taylorjsam/3D-Printed-Wall-Control/Printed Snap Hook Hangers/Park Tool/Park Tool CT-3 (vert) PH.stl

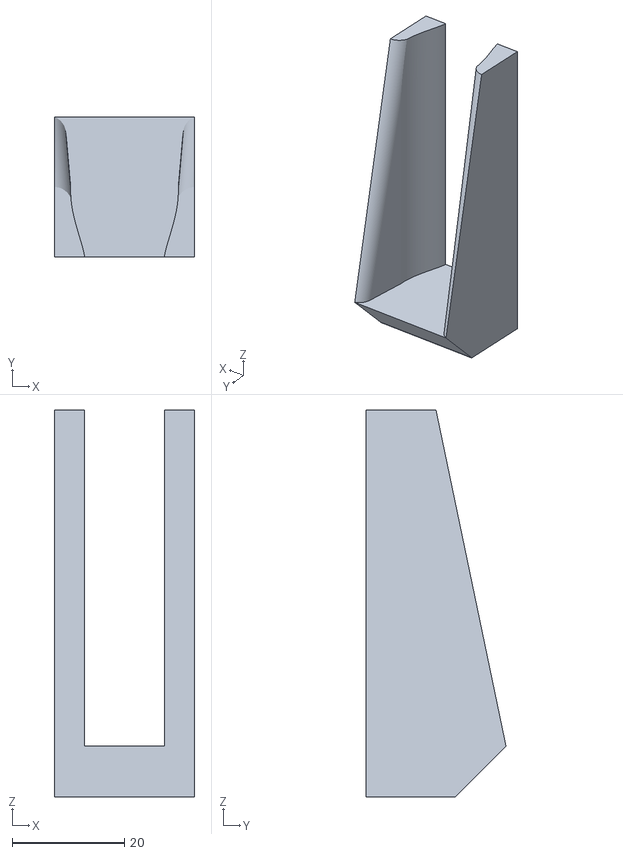
[picture p15: CAD file, 2025-12-08]
Printed Snap Hook Hangers/Park Tool/Park Tool CT-3 (vert) PH.stl
25.0 x 25.0 x 69.1
