taylorjsam/3D-Printed-Wall-Control/Printed Snap Hook Hangers/PB Swiss/PB Swiss 1255 MR PH.stl

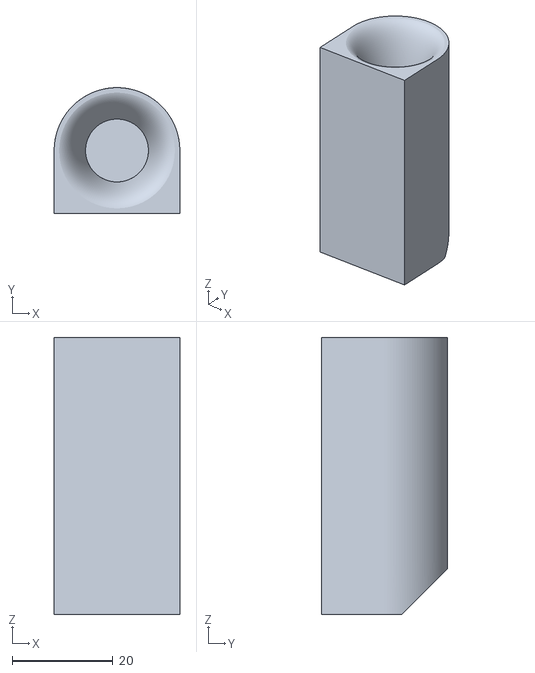
[picture p16: CAD file, 2025-11-05]
Printed Snap Hook Hangers/PB Swiss/PB Swiss 1255 MR PH.stl
25.0 x 25.0 x 55.1
