taylorjsam/3D-Printed-Wall-Control/Printed Snap Hook Hangers/Pedro's/Pedros Cable Cutters (vert)PH.stl

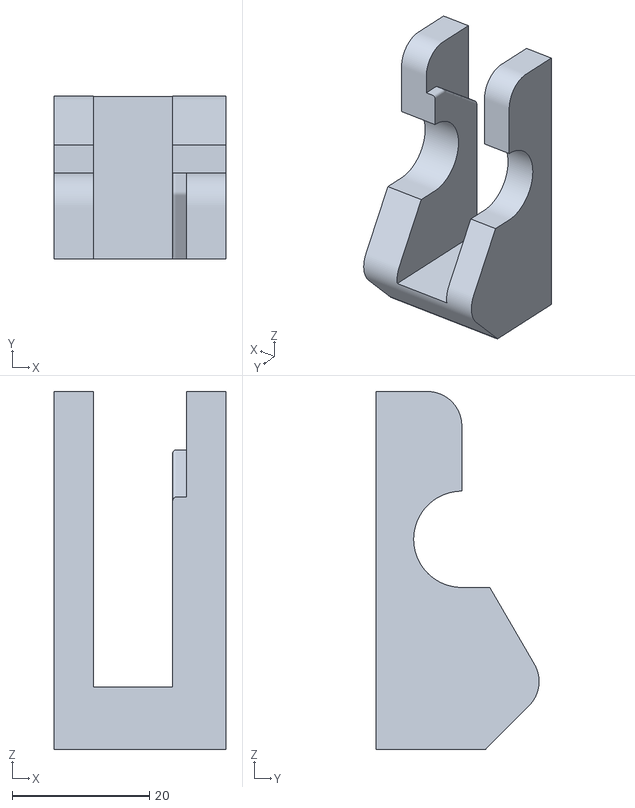
[picture p17: CAD file, 2025-11-06]
Printed Snap Hook Hangers/Pedro's/Pedros Cable Cutters (vert)PH.stl
25.0 x 23.7 x 52.1
