taylorjsam/3D-Printed-Wall-Control/Printed Snap Hook Hangers/Rock Shox/Rock Shox Shock Pump SH.stl

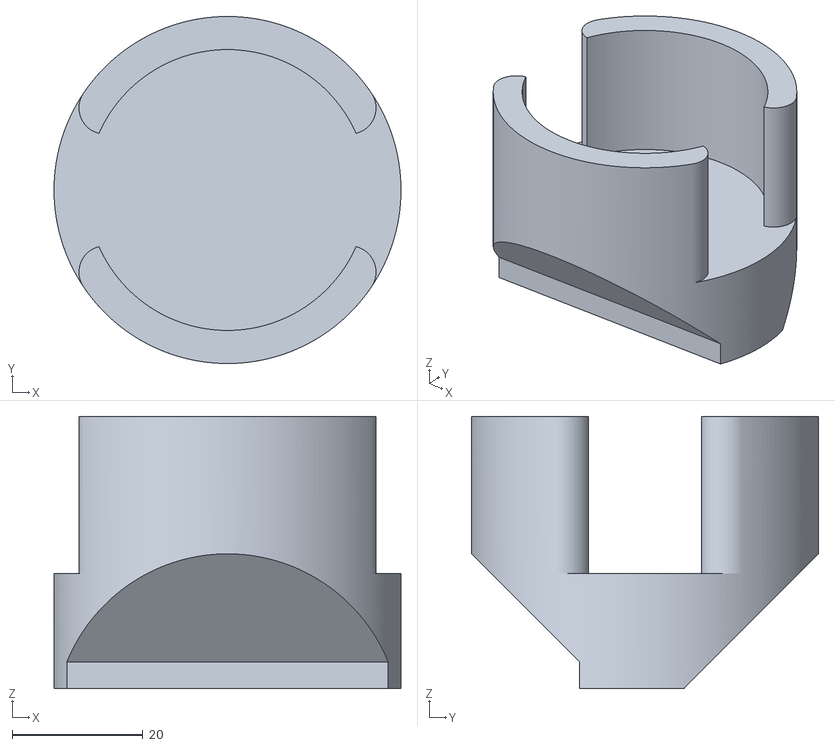
[picture p18: CAD file, 2025-10-18]
Printed Snap Hook Hangers/Rock Shox/Rock Shox Shock Pump SH.stl
53.0 x 53.0 x 41.6
