taylorjsam/3D-Printed-Wall-Control/Printed Snap Hook Hangers/Shimano/Shimano Bleed Funnel PH.stl

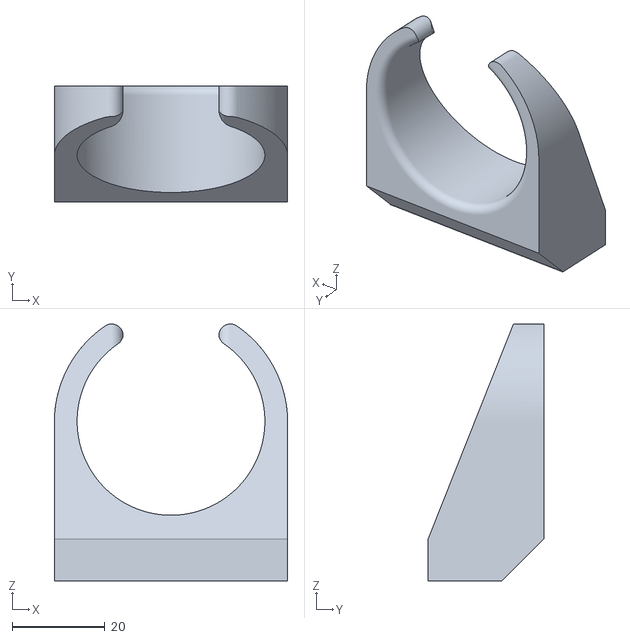
[picture p19: CAD file, 2025-12-08]
Printed Snap Hook Hangers/Shimano/Shimano Bleed Funnel PH.stl
50.4 x 25.0 x 55.5
