taylorjsam/3D-Printed-Wall-Control/Printed Snap Hook Hangers/SK/SK 10 Heavy Duty Scissors PH.stl

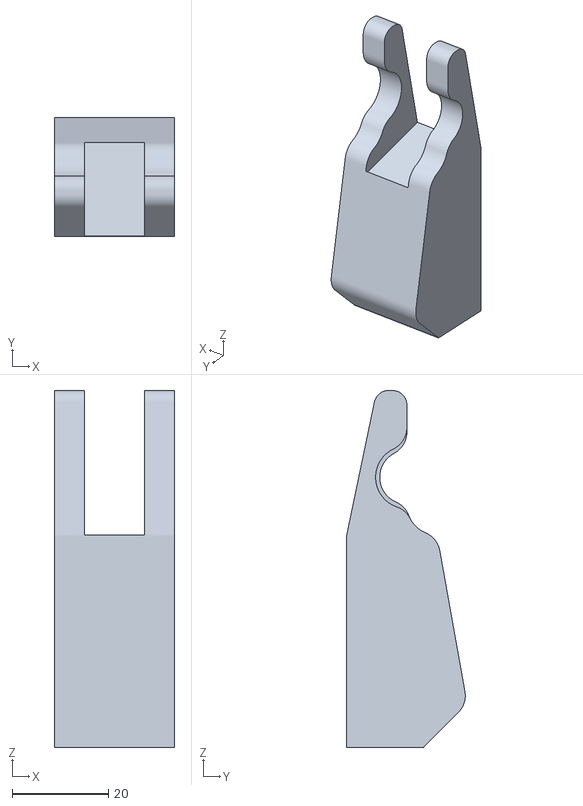
[picture p20: CAD file, 2025-10-25]
Printed Snap Hook Hangers/SK/SK 10 Heavy Duty Scissors PH.stl
25.0 x 24.6 x 74.1
