taylorjsam/3D-Printed-Wall-Control/Printed Snap Hook Hangers/Stan's/Stan's 2oz Bottle.stl

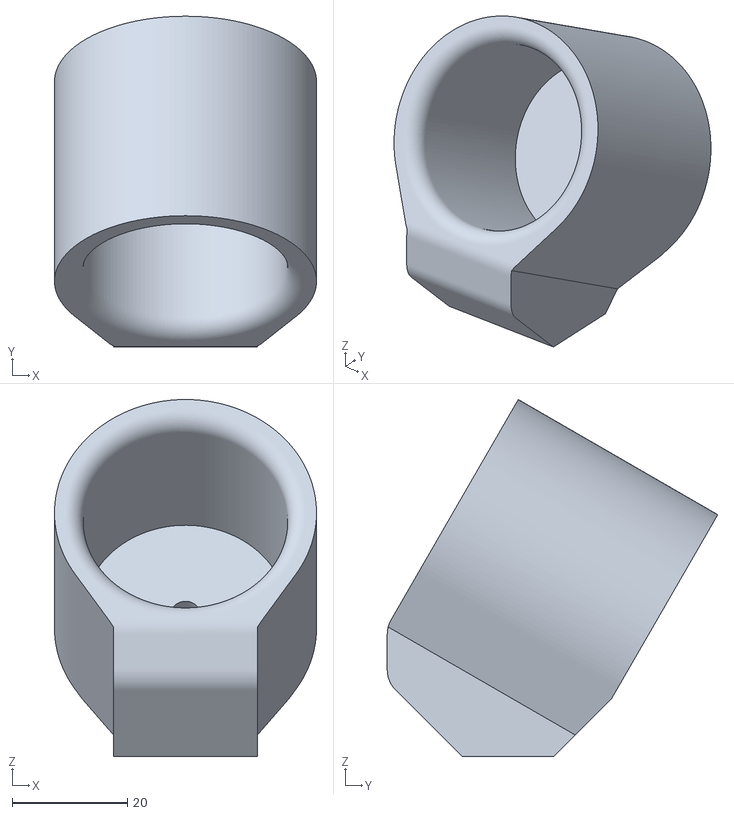
[picture p21: CAD file, 2025-12-18]
Printed Snap Hook Hangers/Stan's/Stan's 2oz Bottle.stl
45.5 x 57.4 x 62.0
