taylorjsam/3D-Printed-Wall-Control/Printed Snap Hook Hangers/Starrett/Starrett 18-C.stl

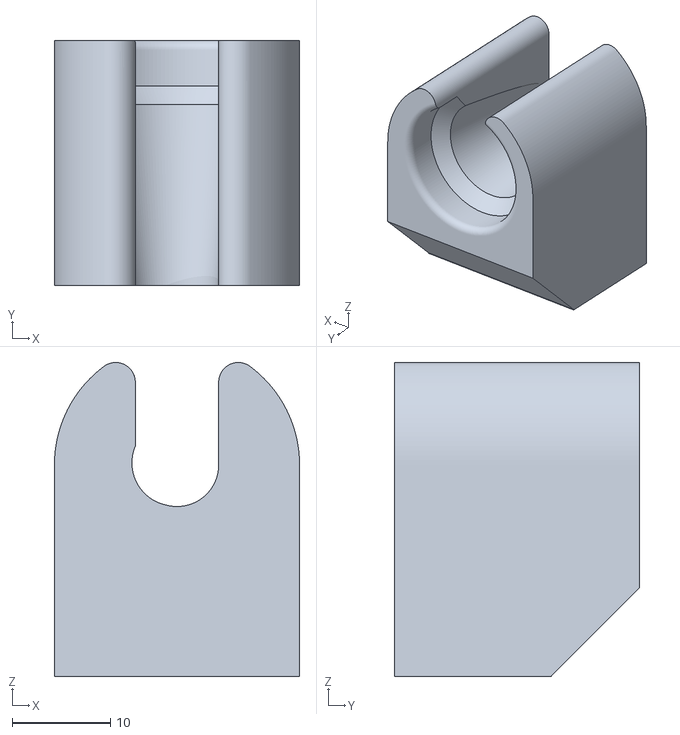
[picture p22: CAD file, 2026-03-05]
Printed Snap Hook Hangers/Starrett/Starrett 18-C.stl
25.0 x 25.0 x 32.0
