taylorjsam/3D-Printed-Wall-Control/Printed Snap Hook Hangers/Vessel/Vessel Megadora 6pc PH.stl

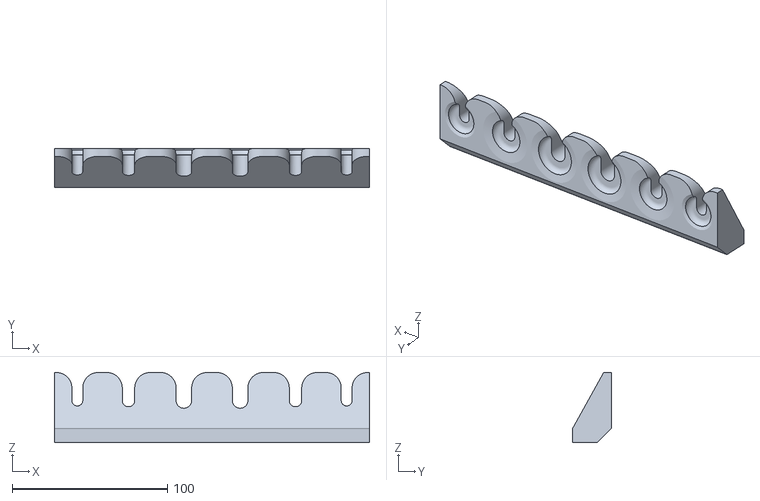
[picture p23: CAD file, 2025-10-19]
Printed Snap Hook Hangers/Vessel/Vessel Megadora 6pc PH.stl
202.8 x 25.0 x 45.1
