taylorjsam/3D-Printed-Wall-Control/Printed Snap Hook Hangers/Wera/Wera 074710 (Adjustable Torque) PH.stl

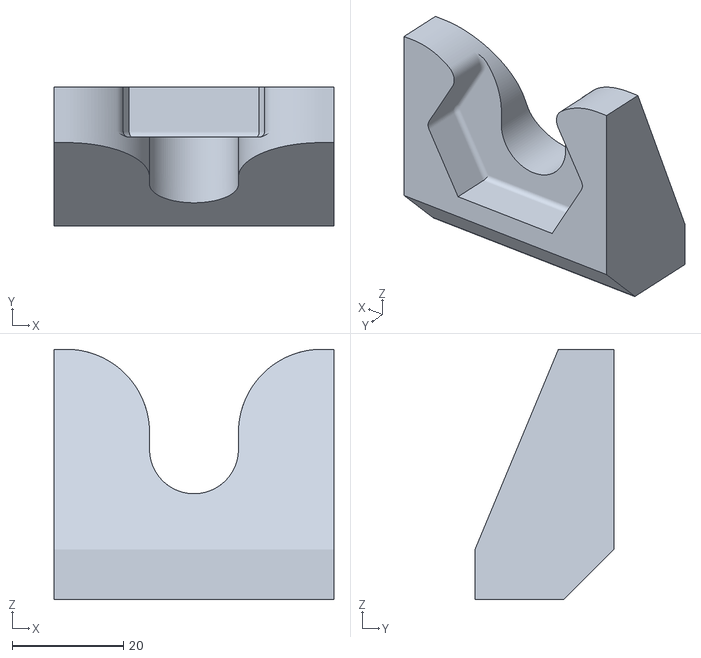
[picture p24: CAD file, 2026-03-10]
Printed Snap Hook Hangers/Wera/Wera 074710 (Adjustable Torque) PH.stl
50.4 x 25.0 x 45.1
