taylorjsam/3D-Printed-Wall-Control/Wall Control Paint Hook/Bernzomatic/Bernzomatic Firepoint Creator Tool.stl

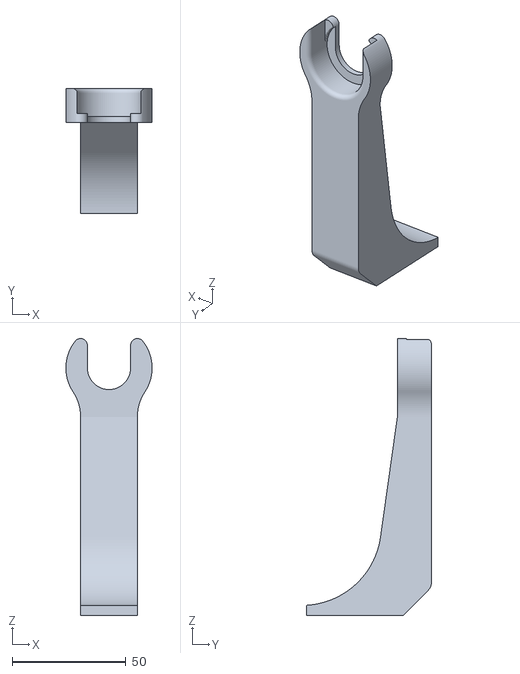
[picture p25: CAD file, 2025-12-18]
Wall Control Paint Hook/Bernzomatic/Bernzomatic Firepoint Creator Tool.stl
38.0 x 55.0 x 122.0
