taylorjsam/3D-Printed-Wall-Control/Wall Control Paint Hook/Milwaukee/M18 Upright v4 (long).stl

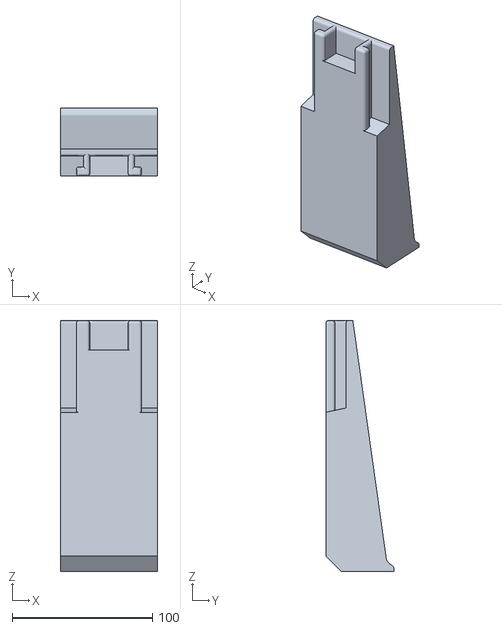
[picture p26: CAD file, 2025-12-08]
Wall Control Paint Hook/Milwaukee/M18 Upright v4 (long).stl
69.0 x 48.8 x 179.0
