taylorjsam/3D-Printed-Wall-Control/Wall Control Small Hook/CooBeast/CooBeast 1:4 Digital Torque Wrench.stl

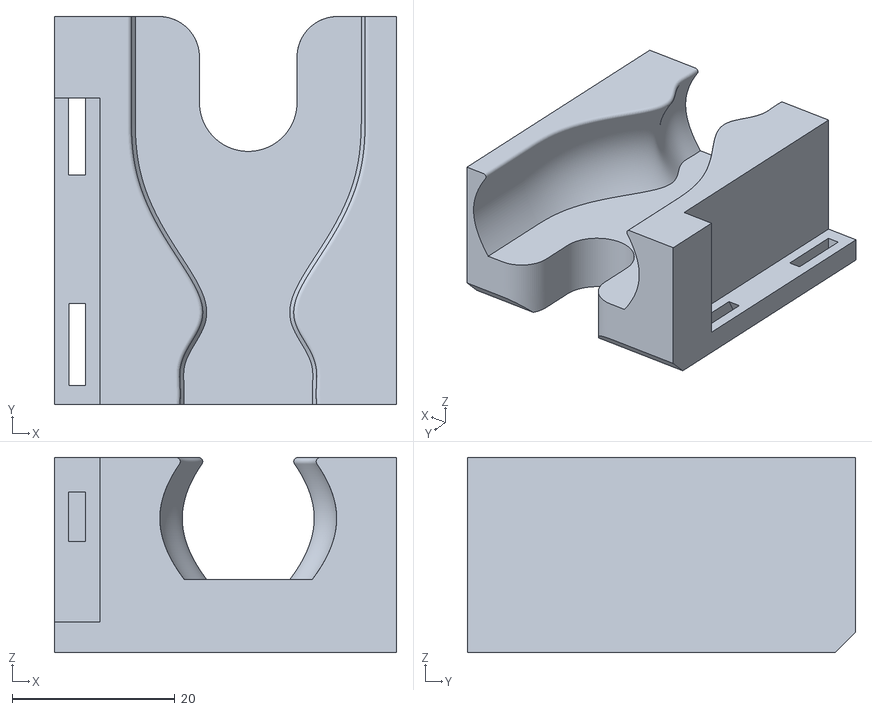
[picture p27: CAD file, 2025-12-20]
Wall Control Small Hook/CooBeast/CooBeast 1:4 Digital Torque Wrench.stl
42.1 x 47.8 x 24.0
