taylorjsam/3D-Printed-Wall-Control/Wall Control Small Hook/epAuto/epAuto 1:2 Torque Wrench.stl

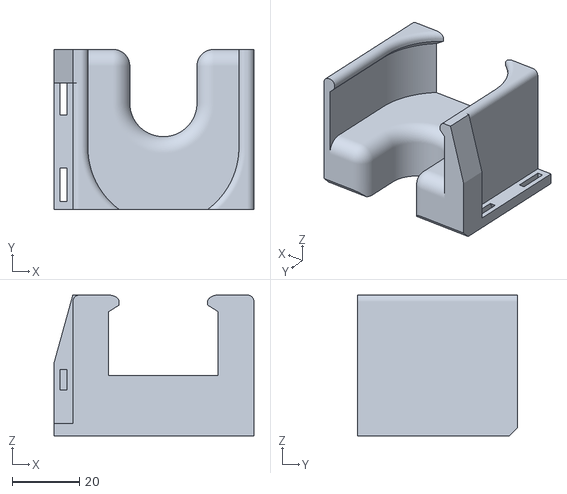
[picture p28: CAD file, 2025-12-20]
Wall Control Small Hook/epAuto/epAuto 1:2 Torque Wrench.stl
59.6 x 47.8 x 42.0
