taylorjsam/3D-Printed-Wall-Control/Wall Control Small Hook/Generic/Angle Grinder Disc Holder v1.stl

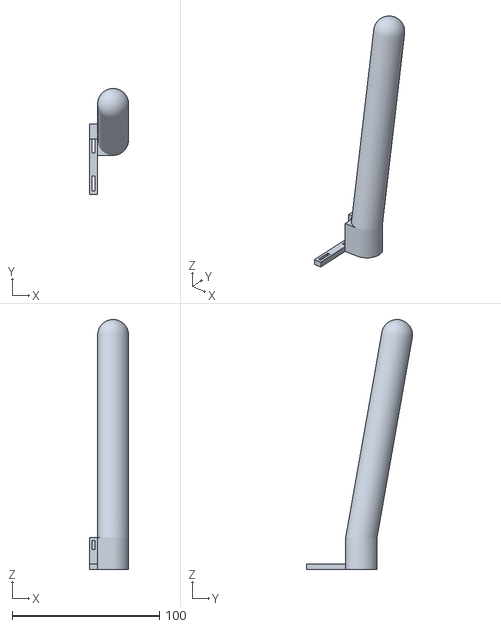
[picture p29: CAD file, 2025-12-08]
Wall Control Small Hook/Generic/Angle Grinder Disc Holder v1.stl
26.6 x 72.0 x 169.6
