taylorjsam/3D-Printed-Wall-Control/Wall Control Small Hook/Ignance/Igance P6 Pro (Single).stl

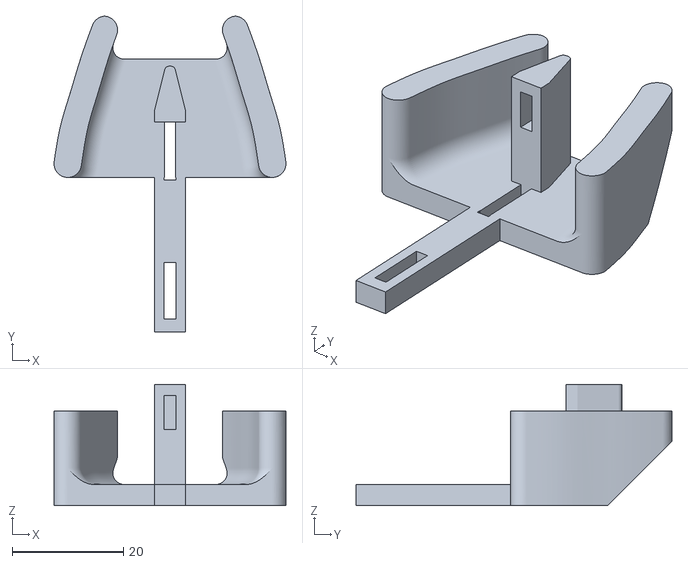
[picture p30: CAD file, 2025-10-04]
Wall Control Small Hook/Ignance/Igance P6 Pro (Single).stl
41.7 x 56.7 x 21.8
