taylorjsam/3D-Printed-Wall-Control/Wall Control Small Hook/Knipex/Knipex Electrician Shears.stl

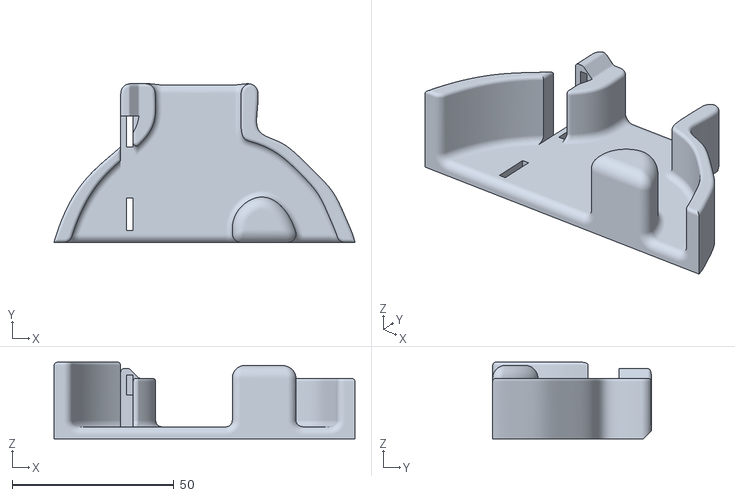
[picture p31: CAD file, 2025-12-08]
Wall Control Small Hook/Knipex/Knipex Electrician Shears.stl
93.1 x 49.0 x 23.8
