taylorjsam/3D-Printed-Wall-Control/Wall Control Small Hook/Park Tool/Park Tool HMR-4.stl

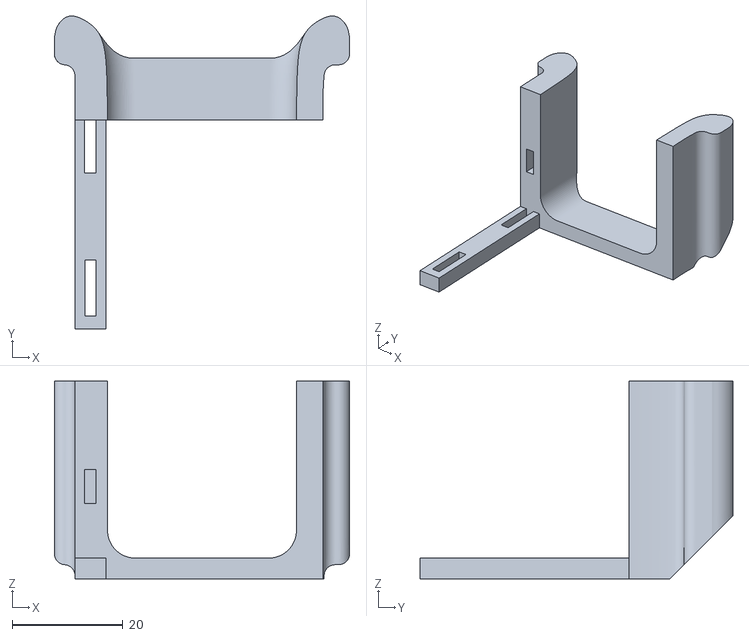
[picture p32: CAD file, 2025-10-07]
Wall Control Small Hook/Park Tool/Park Tool HMR-4.stl
53.4 x 56.6 x 35.8
