taylorjsam/3D-Printed-Wall-Control/Wall Control Small Hook/Pedros/Pedros Cable Cutters.stl

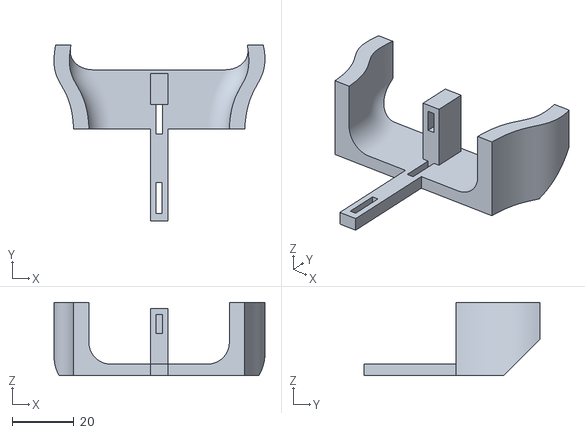
[picture p33: CAD file, 2025-10-04]
Wall Control Small Hook/Pedros/Pedros Cable Cutters.stl
68.4 x 57.0 x 23.8
