taylorjsam/3D-Printed-Wall-Control/Wall Control Small Hook/Rock Shox/Rock Shox Shock Pump.stl

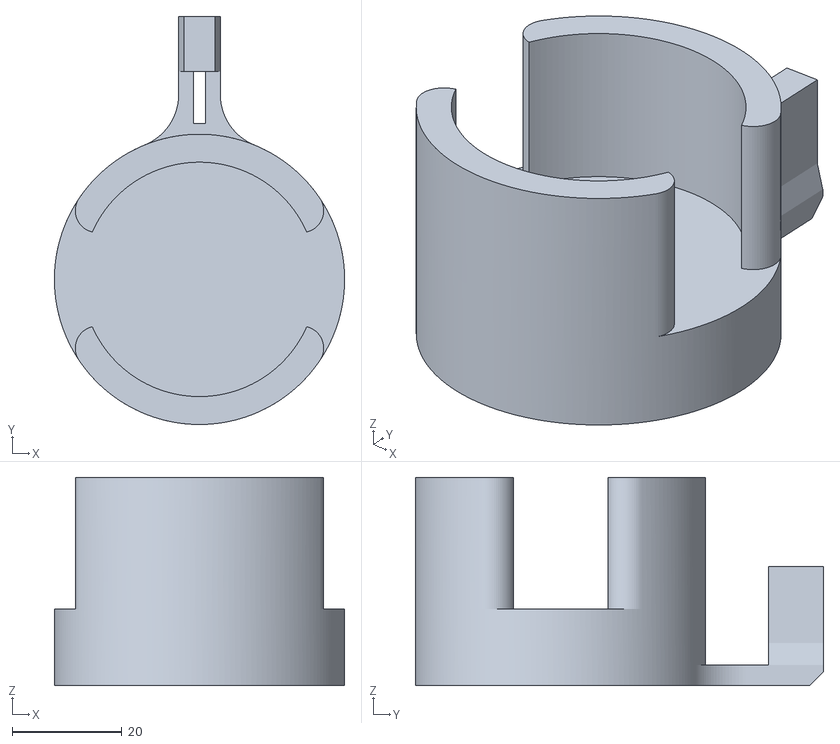
[picture p34: CAD file, 2025-10-04]
Wall Control Small Hook/Rock Shox/Rock Shox Shock Pump.stl
53.0 x 74.5 x 38.0
