taylorjsam/3D-Printed-Wall-Control/Wall Control Small Hook/SK/SK 8in Shears.stl

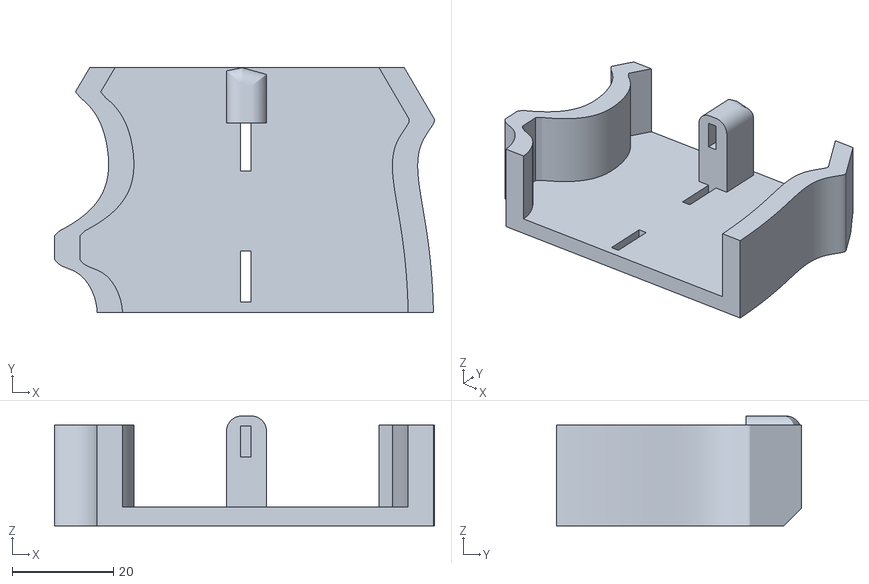
[picture p35: CAD file, 2025-10-10]
Wall Control Small Hook/SK/SK 8in Shears.stl
75.2 x 48.4 x 21.8
