taylorjsam/3D-Printed-Wall-Control/Wall Control Small Hook/Wera/Wera Hex Plus Allen Set.stl

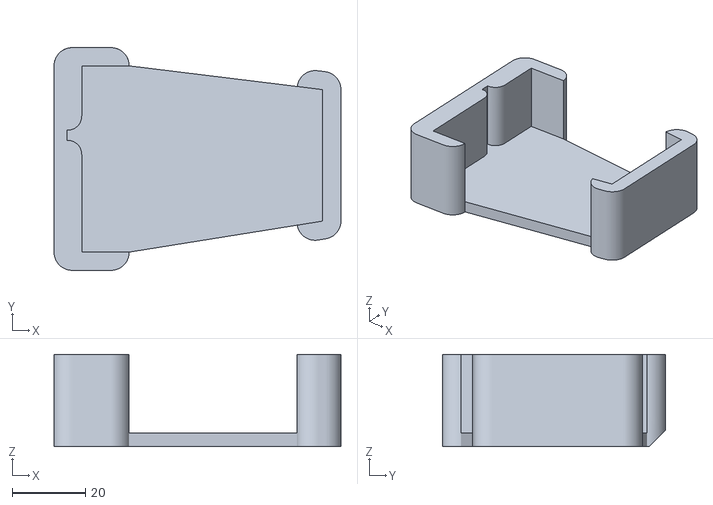
[picture p36: CAD file, 2025-10-07]
Wall Control Small Hook/Wera/Wera Hex Plus Allen Set.stl
78.6 x 61.0 x 25.3
