taylorjsam/3D-Printed-Wall-Control/Printed Snap Hook Hangers/Generic/Adjustable Wrenches/Adjustable Wrench 10mm (vert) PH.stl

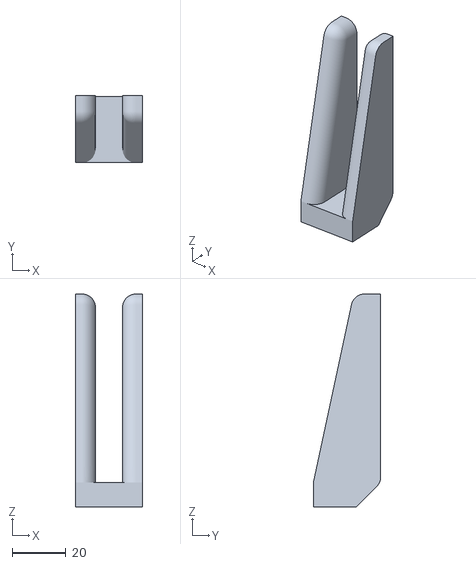
[picture p37: CAD file, 2025-12-08]
Printed Snap Hook Hangers/Generic/Adjustable Wrenches/Adjustable Wrench 10mm (vert) PH.stl
25.0 x 25.0 x 79.1
