taylorjsam/3D-Printed-Wall-Control/Printed Snap Hook Hangers/Generic/Socket Drive Accessories/2x 1:4 Drive Male Narrow.stl

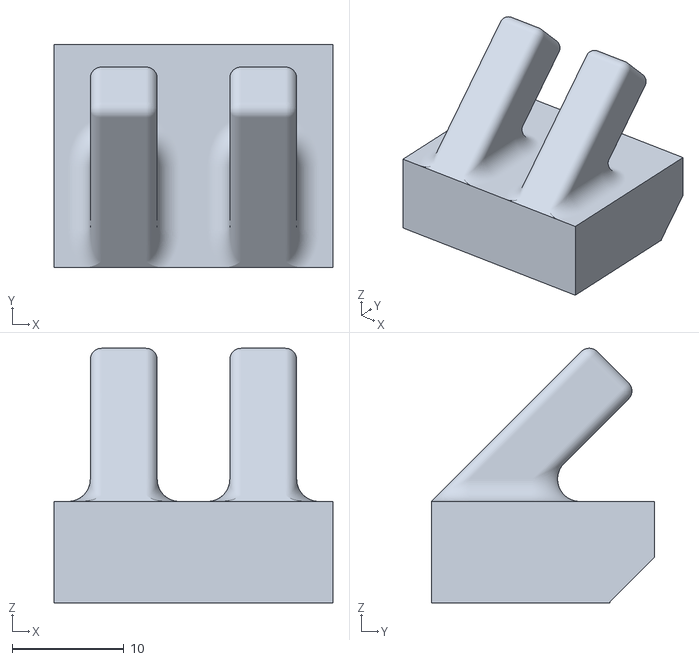
[picture p38: CAD file, 2025-12-20]
Printed Snap Hook Hangers/Generic/Socket Drive Accessories/2x 1:4 Drive Male Narrow.stl
25.0 x 20.0 x 22.8
