taylorjsam/3D-Printed-Wall-Control/Printed Snap Hook Hangers/Knipex/Knipex 8551250 (vert) PH.stl

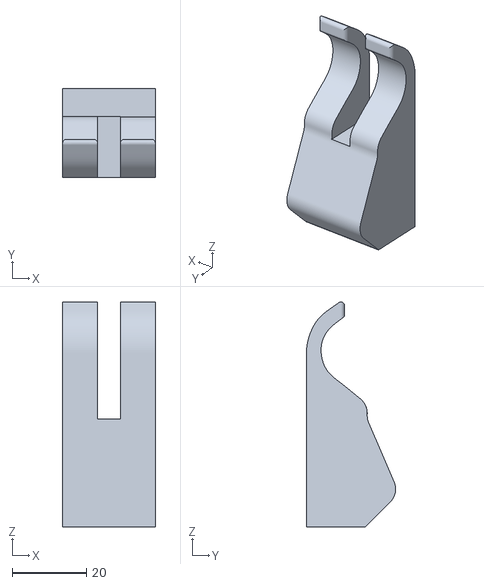
[picture p39: CAD file, 2025-10-23]
Printed Snap Hook Hangers/Knipex/Knipex 8551250 (vert) PH.stl
25.0 x 24.1 x 60.7
