taylorjsam/3D-Printed-Wall-Control/Printed Snap Hook Hangers/Milwaukee/Milwaukee 48-22-3410 PH.stl.stl

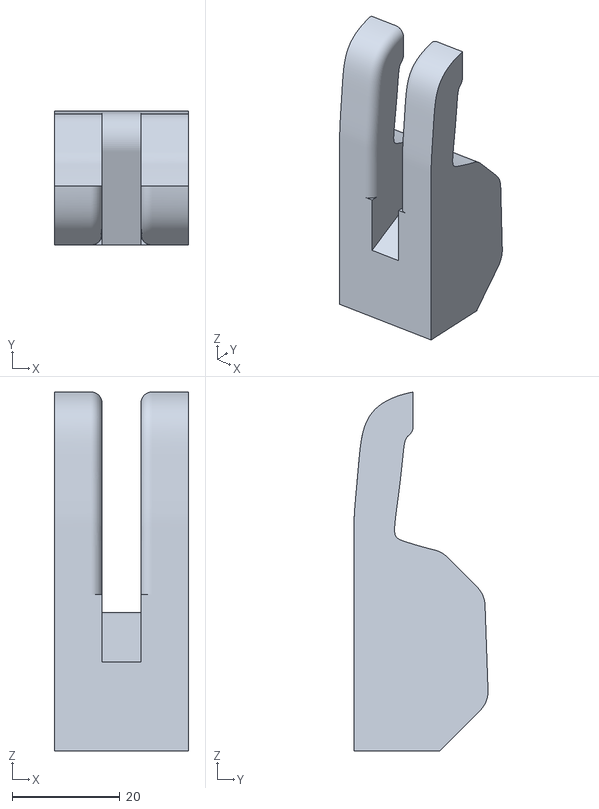
[picture p40: CAD file, 2025-10-25]
Printed Snap Hook Hangers/Milwaukee/Milwaukee 48-22-3410 PH.stl.stl
25.0 x 24.9 x 66.7
