taylorjsam/3D-Printed-Wall-Control/Printed Snap Hook Hangers/Park Tool/Park Tool CT-3 PH.stl

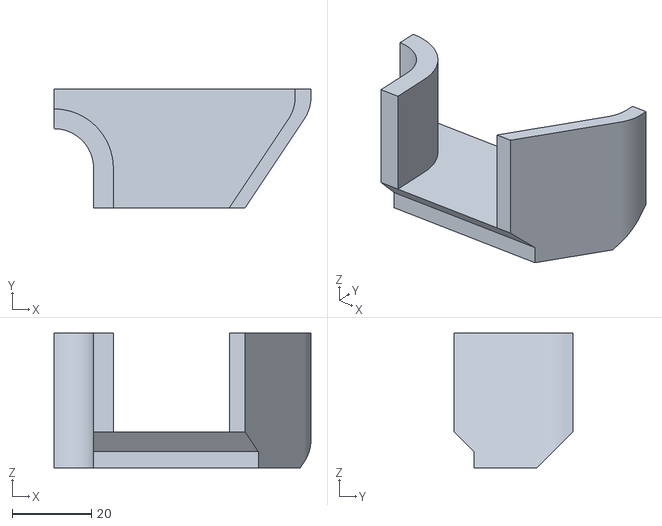
[picture p41: CAD file, 2025-11-06]
Printed Snap Hook Hangers/Park Tool/Park Tool CT-3 PH.stl
65.0 x 30.0 x 34.1
