taylorjsam/3D-Printed-Wall-Control/Printed Snap Hook Hangers/PB Swiss/PB Swiss 4pc PH-PZ PH.stl

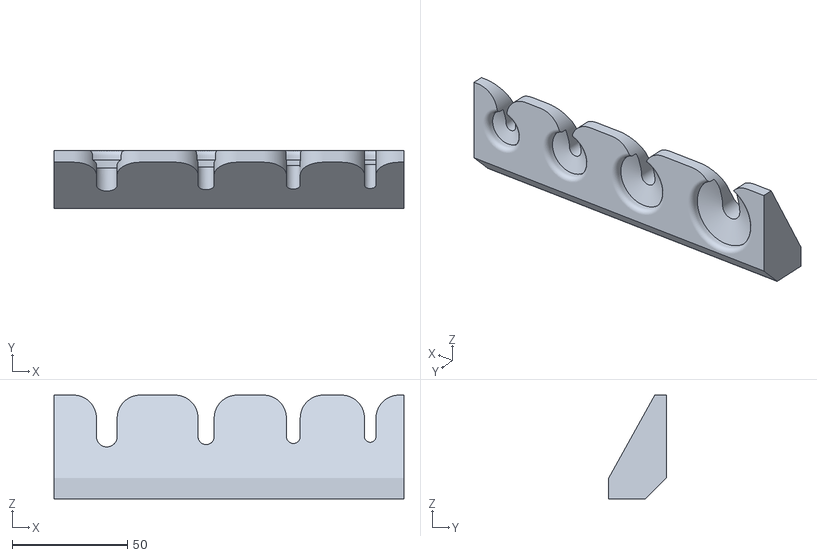
[picture p42: CAD file, 2025-10-24]
Printed Snap Hook Hangers/PB Swiss/PB Swiss 4pc PH-PZ PH.stl
152.0 x 25.0 x 45.1
