taylorjsam/3D-Printed-Wall-Control/Printed Snap Hook Hangers/Pedro's/Pedro's Downhill Tire Lever.stl

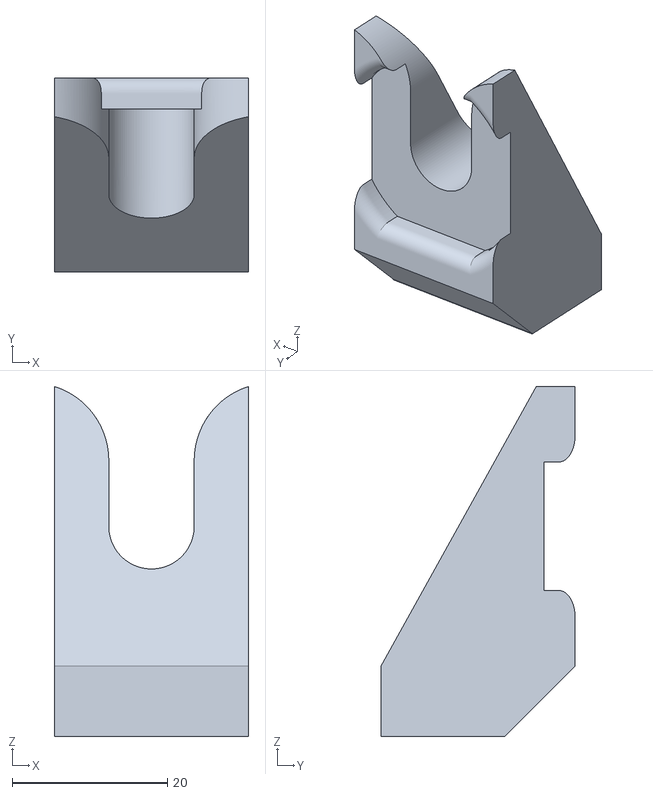
[picture p43: CAD file, 2025-10-18]
Printed Snap Hook Hangers/Pedro's/Pedro's Downhill Tire Lever.stl
25.0 x 25.0 x 45.1
