taylorjsam/3D-Printed-Wall-Control/Printed Snap Hook Hangers/SK/SK 8" Heavy Duty Cutters PH.stl

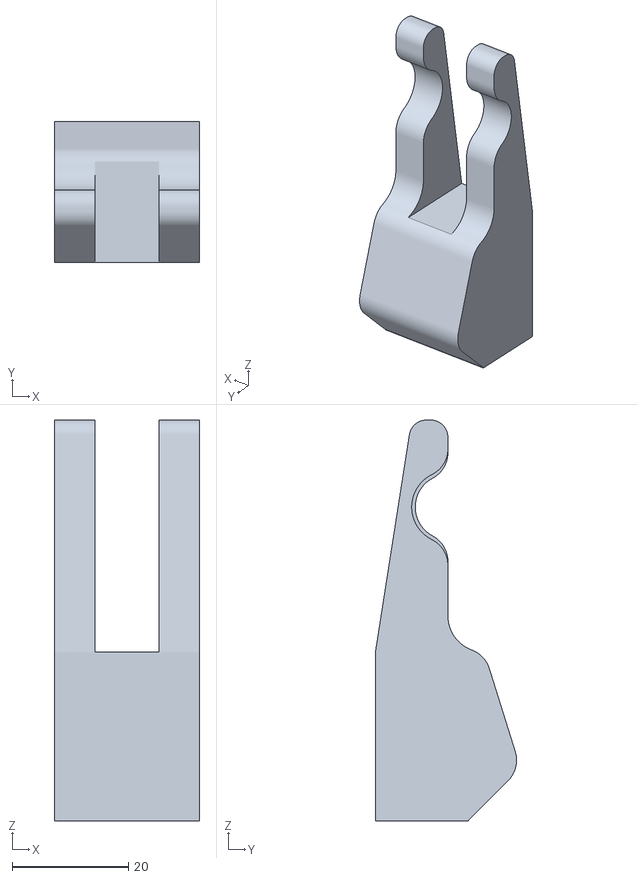
[picture p44: CAD file, 2025-10-24]
Printed Snap Hook Hangers/SK/SK 8" Heavy Duty Cutters PH.stl
25.0 x 24.3 x 69.1
