taylorjsam/3D-Printed-Wall-Control/Printed Snap Hook Hangers/Snap On/Snap On AWSG800 PH.stl

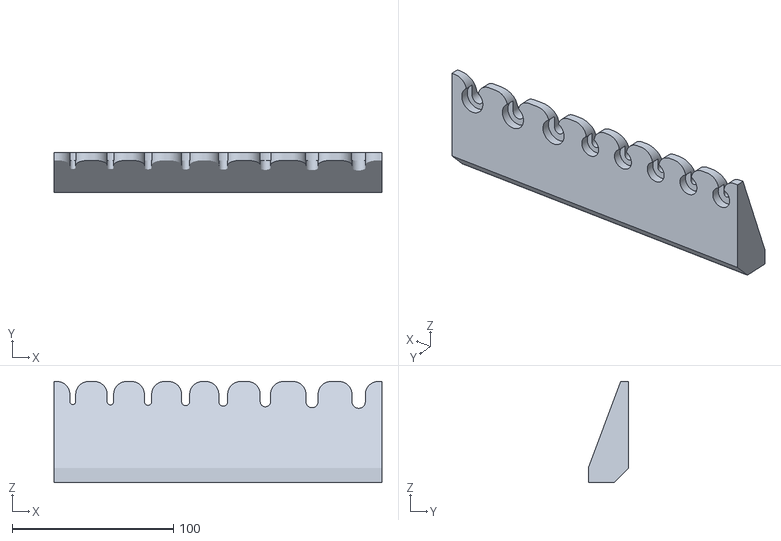
[picture p45: CAD file, 2025-11-05]
Printed Snap Hook Hangers/Snap On/Snap On AWSG800 PH.stl
203.2 x 25.0 x 62.6
