taylorjsam/3D-Printed-Wall-Control/Printed Snap Hook Hangers/Stan's/Stan's Core Remover.stl

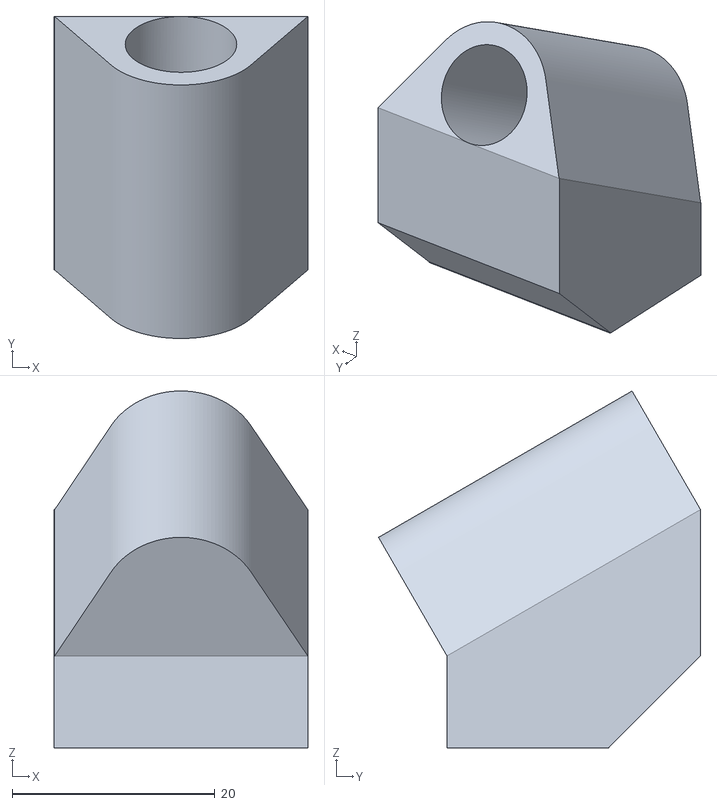
[picture p46: CAD file, 2025-10-18]
Printed Snap Hook Hangers/Stan's/Stan's Core Remover.stl
25.0 x 31.7 x 35.2
