taylorjsam/3D-Printed-Wall-Control/Printed Snap Hook Hangers/Vessel/Megadora P0-S4 add-on PH.stl

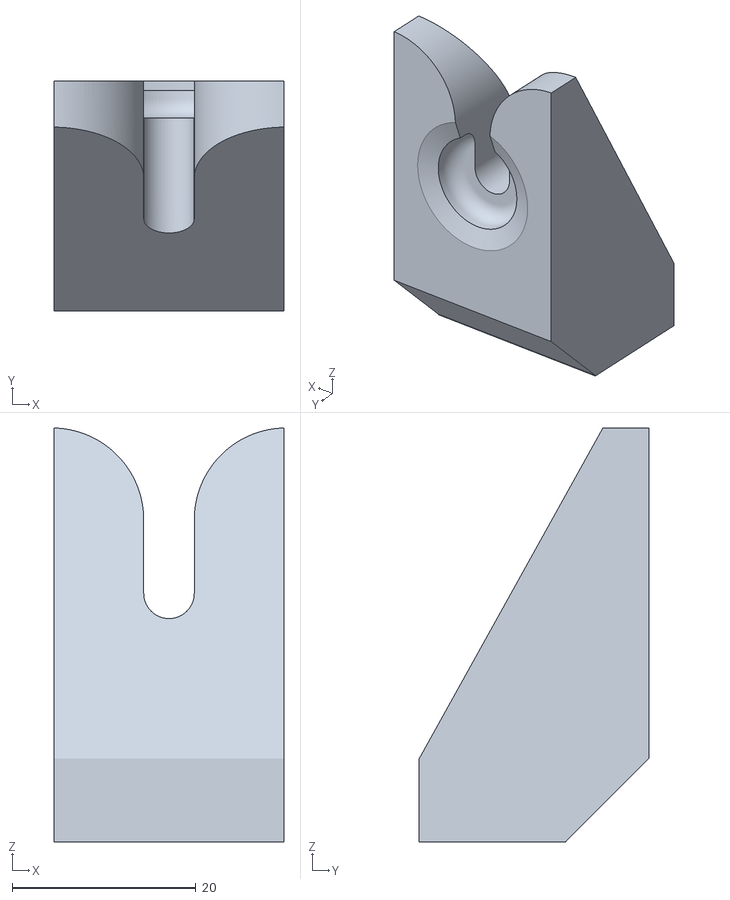
[picture p47: CAD file, 2025-10-18]
Printed Snap Hook Hangers/Vessel/Megadora P0-S4 add-on PH.stl
25.0 x 25.0 x 45.1
