taylorjsam/3D-Printed-Wall-Control/Wall Control Paint Hook/Milwaukee/M18 Upright v4 (angled 27.5).stl

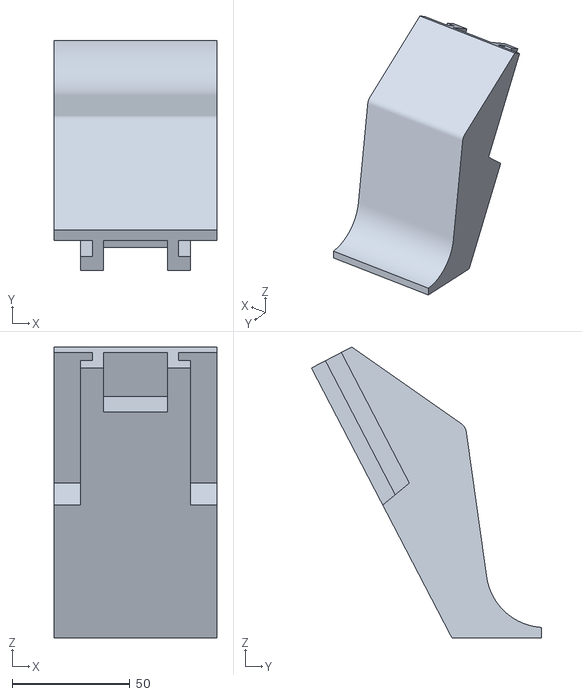
[picture p48: CAD file, 2025-12-08]
Wall Control Paint Hook/Milwaukee/M18 Upright v4 (angled 27.5).stl
69.0 x 97.6 x 123.3
