taylorjsam/3D-Printed-Wall-Control/Wall Control Small Hook/Generic/Mason Jar Wide Mouth Mount (small hook) v5.stl

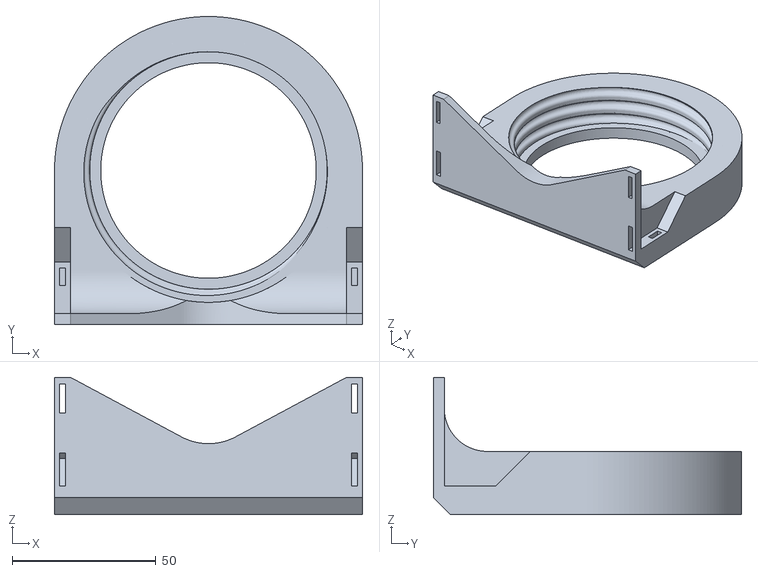
[picture p49: CAD file, 2025-12-08]
Wall Control Small Hook/Generic/Mason Jar Wide Mouth Mount (small hook) v5.stl
107.2 x 107.2 x 47.8
