taylorjsam/3D-Printed-Wall-Control/Wall Control Small Hook/Ignance/Igance P6 Pro (Double).stl

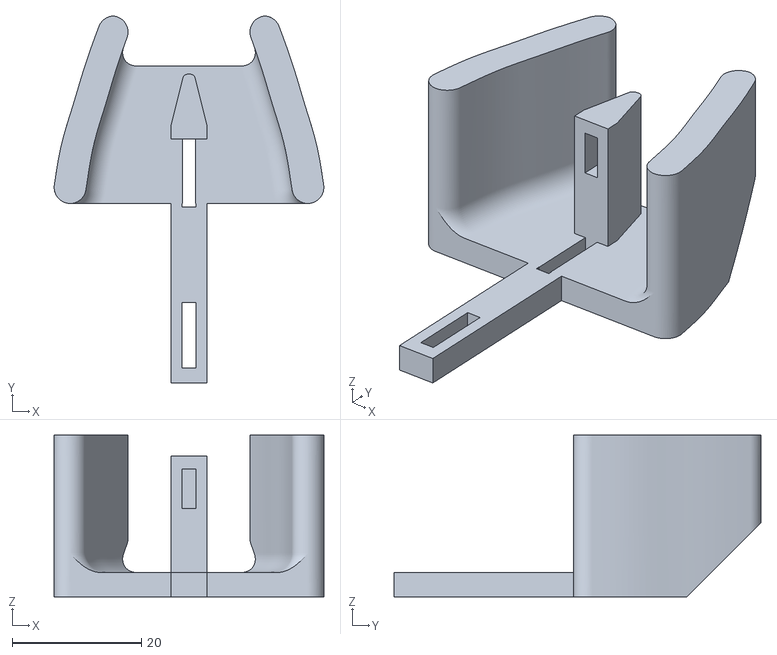
[picture p50: CAD file, 2025-10-04]
Wall Control Small Hook/Ignance/Igance P6 Pro (Double).stl
41.7 x 56.7 x 25.0
