taylorjsam/3D-Printed-Wall-Control/Wall Control Small Hook/Park Tool/Park Tool CCP-22.stl

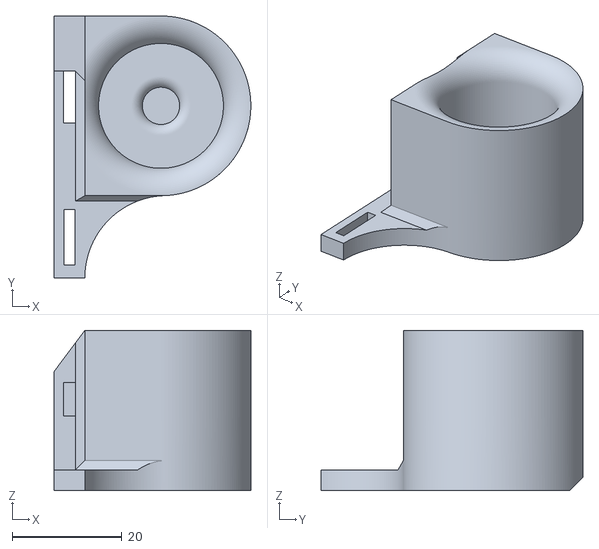
[picture p51: CAD file, 2025-10-07]
Wall Control Small Hook/Park Tool/Park Tool CCP-22.stl
35.9 x 47.8 x 29.3
