taylorjsam/3D-Printed-Wall-Control/Wall Control Small Hook/SK/SK 10in Scissors.stl

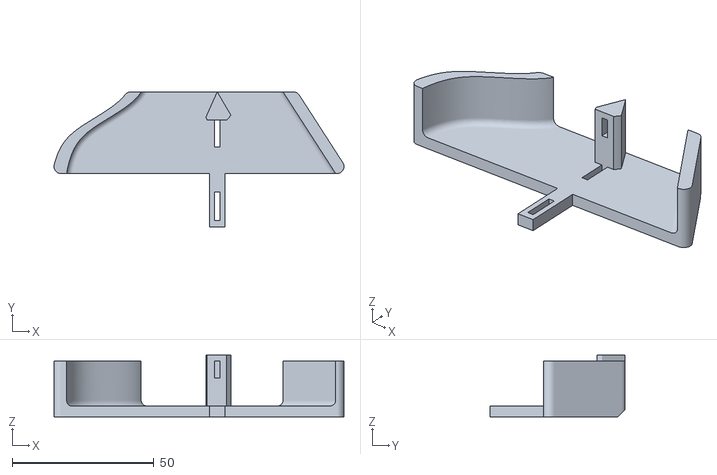
[picture p52: CAD file, 2025-10-07]
Wall Control Small Hook/SK/SK 10in Scissors.stl
102.3 x 47.8 x 21.8
