taylorjsam/3D-Printed-Wall-Control/Printed Snap Hook Hangers/Generic/Adjustable Wrenches/Adjustable Wrench 9mm (vert) PH.stl.stl

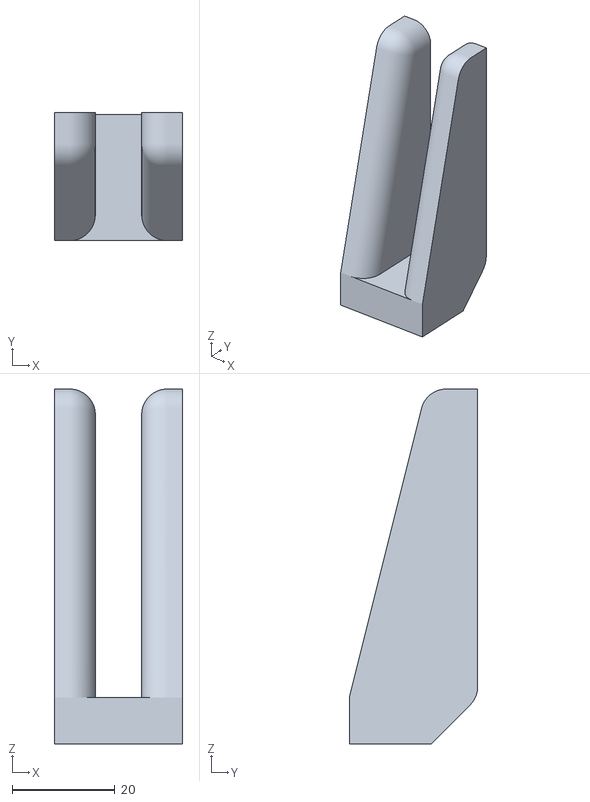
[picture p53: CAD file, 2025-12-08]
Printed Snap Hook Hangers/Generic/Adjustable Wrenches/Adjustable Wrench 9mm (vert) PH.stl.stl
25.0 x 25.0 x 69.1
