taylorjsam/3D-Printed-Wall-Control/Printed Snap Hook Hangers/Generic/Angle Grinder (wrench) PH.stl

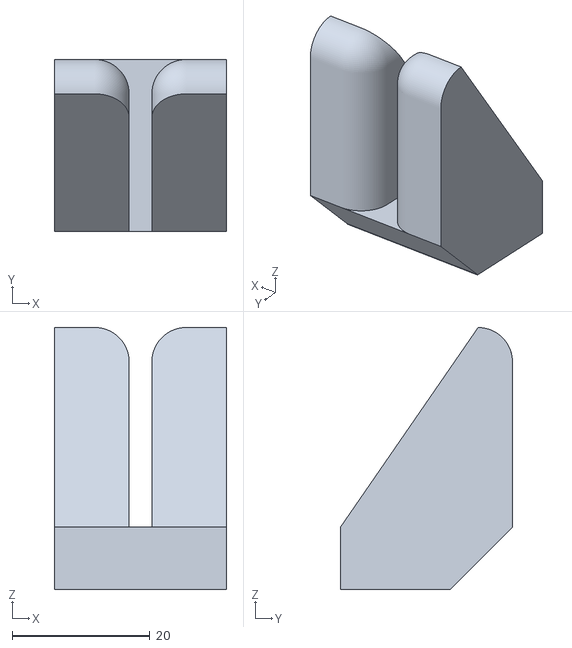
[picture p54: CAD file, 2025-12-08]
Printed Snap Hook Hangers/Generic/Angle Grinder (wrench) PH.stl
25.0 x 25.0 x 38.1
