taylorjsam/3D-Printed-Wall-Control/Printed Snap Hook Hangers/Generic/Hammers (hold by head face)/31.5mm Hammer PH.stl

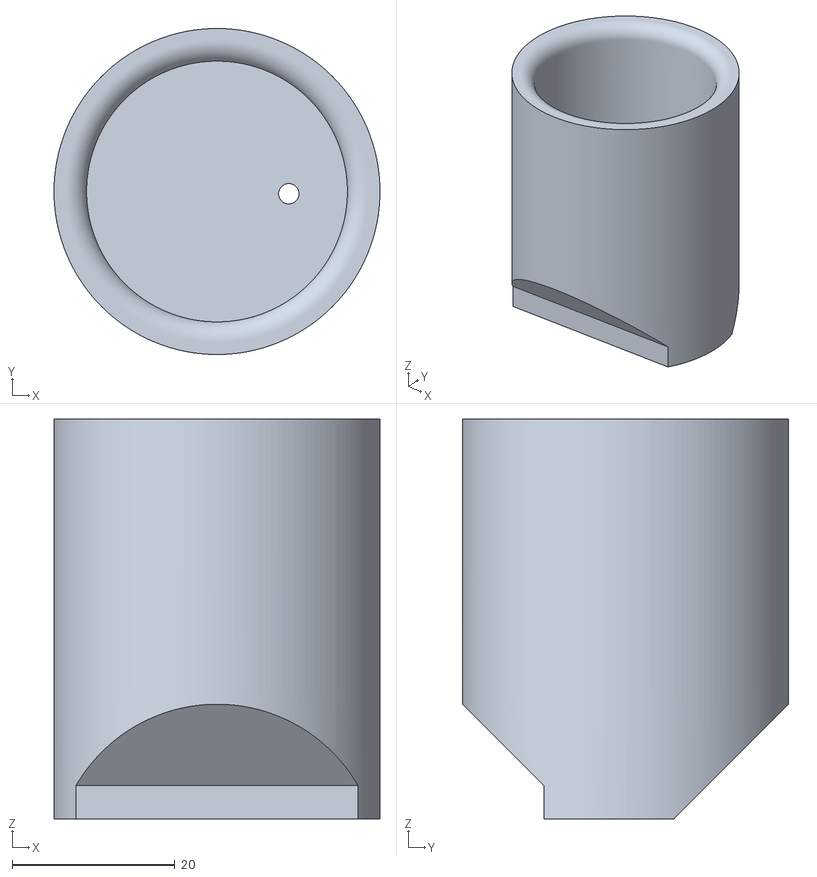
[picture p55: CAD file, 2025-10-25]
Printed Snap Hook Hangers/Generic/Hammers (hold by head face)/31.5mm Hammer PH.stl
40.0 x 40.0 x 49.1
