taylorjsam/3D-Printed-Wall-Control/Printed Snap Hook Hangers/Knipex/Knipex 8602250 (vert) PH.stl

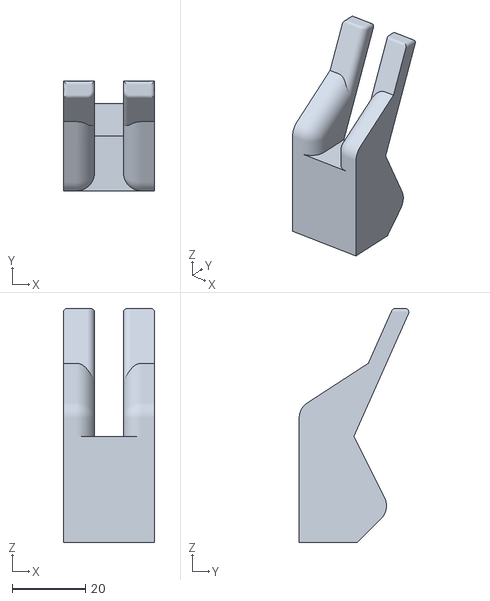
[picture p56: CAD file, 2025-10-23]
Printed Snap Hook Hangers/Knipex/Knipex 8602250 (vert) PH.stl
25.0 x 30.0 x 64.1
