taylorjsam/3D-Printed-Wall-Control/Printed Snap Hook Hangers/Milwaukee/Milwaukee 48-22-3407 PH.stl

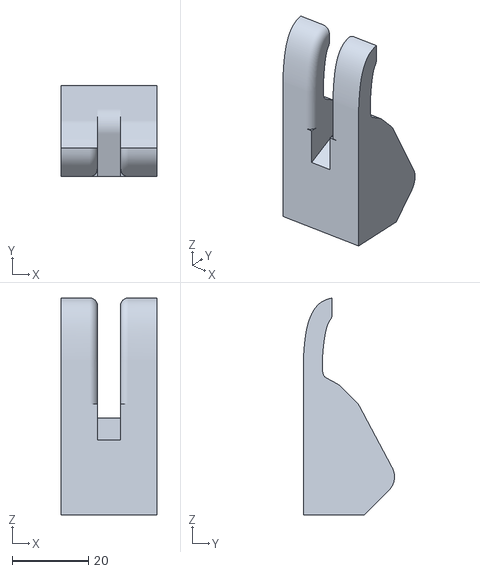
[picture p57: CAD file, 2025-10-25]
Printed Snap Hook Hangers/Milwaukee/Milwaukee 48-22-3407 PH.stl
25.0 x 23.8 x 56.8
