taylorjsam/3D-Printed-Wall-Control/Printed Snap Hook Hangers/Park Tool/Park Tool NP-6 (vert) PH.stl

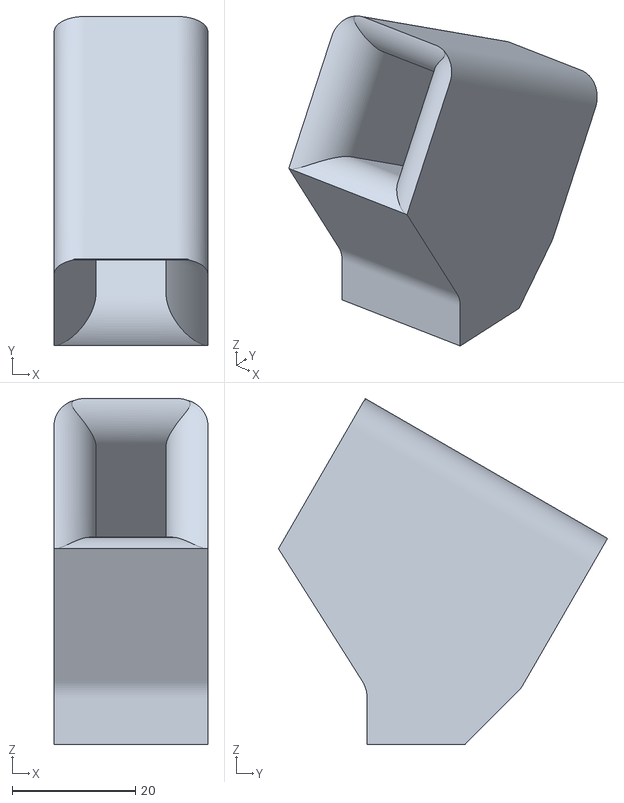
[picture p58: CAD file, 2025-11-06]
Printed Snap Hook Hangers/Park Tool/Park Tool NP-6 (vert) PH.stl
25.0 x 53.5 x 56.3
