taylorjsam/3D-Printed-Wall-Control/Printed Snap Hook Hangers/Wera/Wera 392 (flex shaft bit holder) PH.stl

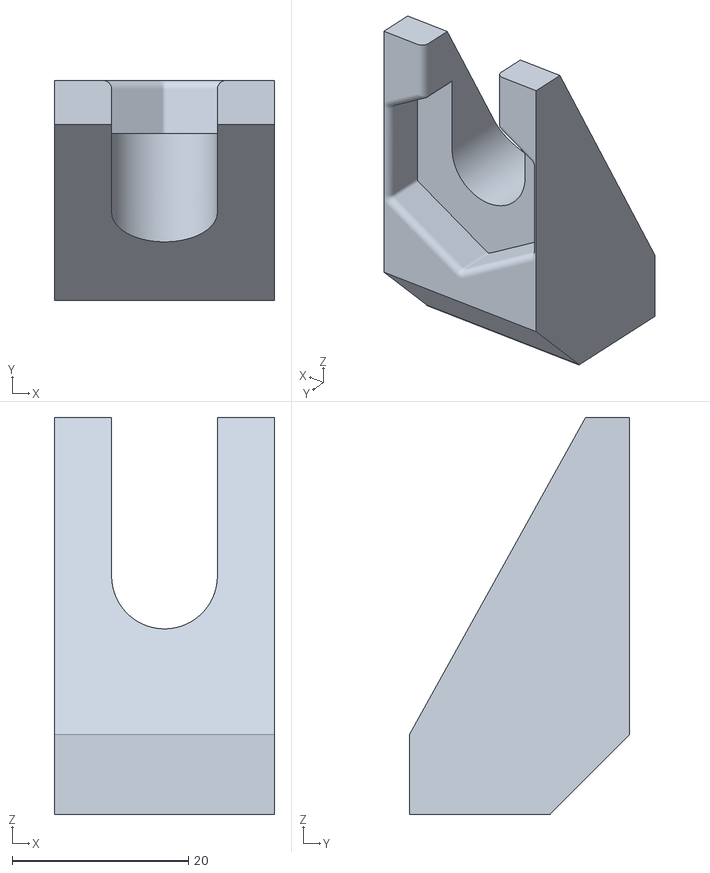
[picture p59: CAD file, 2025-12-08]
Printed Snap Hook Hangers/Wera/Wera 392 (flex shaft bit holder) PH.stl
25.0 x 25.0 x 45.1
