taylorjsam/3D-Printed-Wall-Control/Wall Control Small Hook/Generic/Angle Grinder.stl

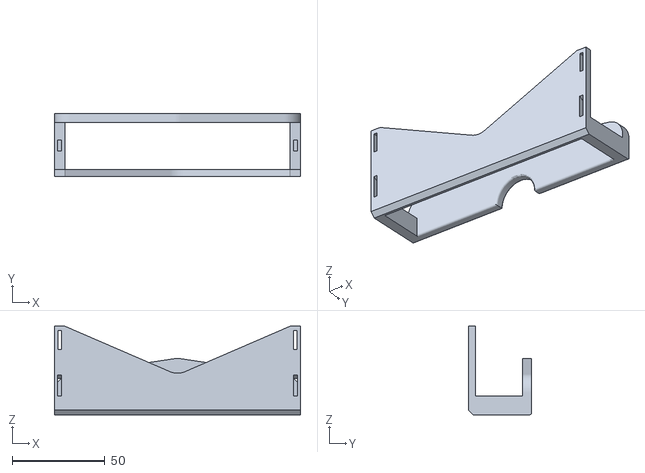
[picture p61: CAD file, 2025-12-08]
Wall Control Small Hook/Generic/Angle Grinder.stl
132.6 x 34.0 x 47.8
