taylorjsam/3D-Printed-Wall-Control/Wall Control Small Hook/Park Tool/Park Tool PW-3 WC.stl

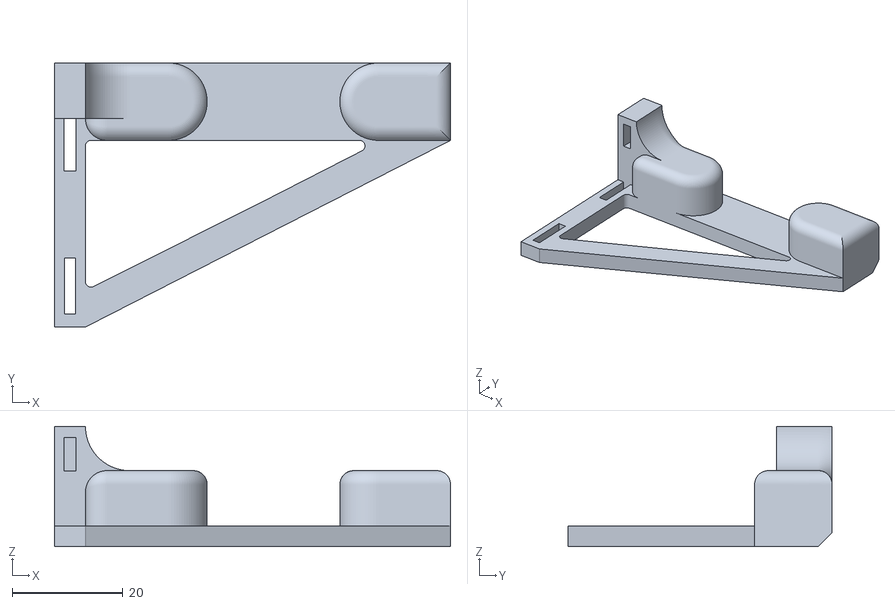
[picture p62: CAD file, 2025-10-06]
Wall Control Small Hook/Park Tool/Park Tool PW-3 WC.stl
71.6 x 47.8 x 21.8
