taylorjsam/3D-Printed-Wall-Control/Printed Snap Hook Hangers/Generic/RaceRide Alu Funnel PH.stl

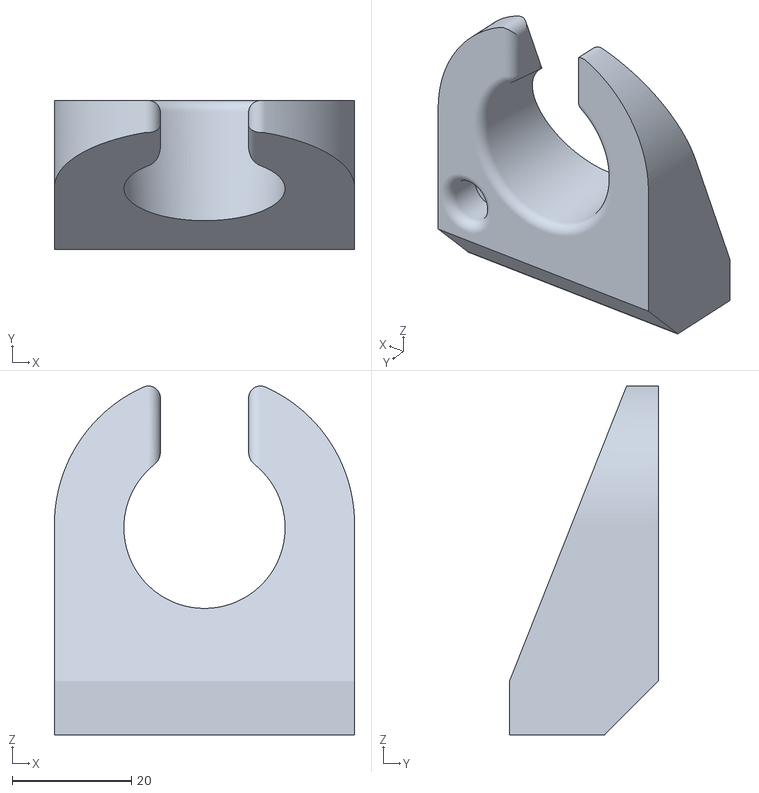
[picture p63: CAD file, 2025-12-08]
Printed Snap Hook Hangers/Generic/RaceRide Alu Funnel PH.stl
50.4 x 25.0 x 58.6
