taylorjsam/3D-Printed-Wall-Control/Printed Snap Hook Hangers/Knipex/Knipex 7412180 (vert) PH.stl

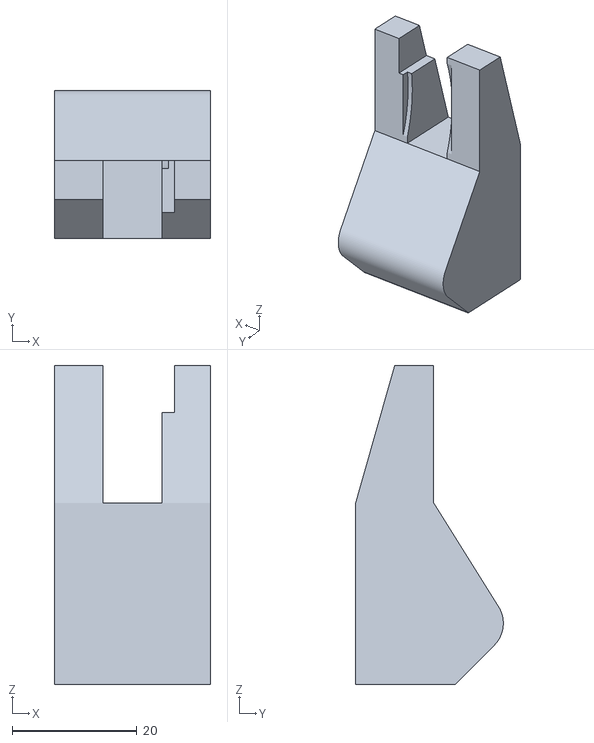
[picture p65: CAD file, 2025-10-23]
Printed Snap Hook Hangers/Knipex/Knipex 7412180 (vert) PH.stl
25.0 x 23.7 x 51.1
