taylorjsam/3D-Printed-Wall-Control/Printed Snap Hook Hangers/Milwaukee/Milwaukee 48-22-3409 PH.stl

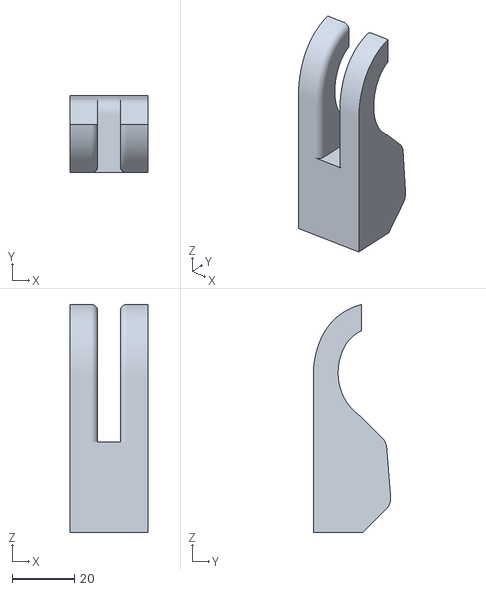
[picture p66: CAD file, 2025-10-24]
Printed Snap Hook Hangers/Milwaukee/Milwaukee 48-22-3409 PH.stl
25.0 x 24.8 x 73.1
