taylorjsam/3D-Printed-Wall-Control/Printed Snap Hook Hangers/Park Tool/Park Tool MLP-1.2 (vert) PH.stl

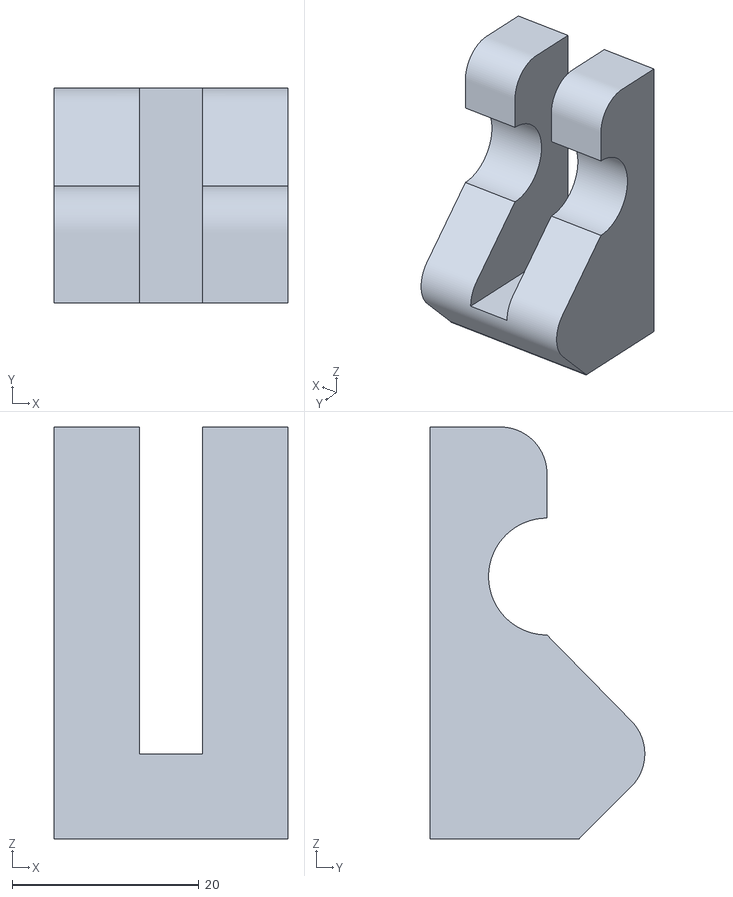
[picture p67: CAD file, 2025-11-06]
Printed Snap Hook Hangers/Park Tool/Park Tool MLP-1.2 (vert) PH.stl
25.0 x 23.0 x 44.1
