taylorjsam/3D-Printed-Wall-Control/Wall Control Small Hook/Park Tool/Park Tool MLP-1.2.stl

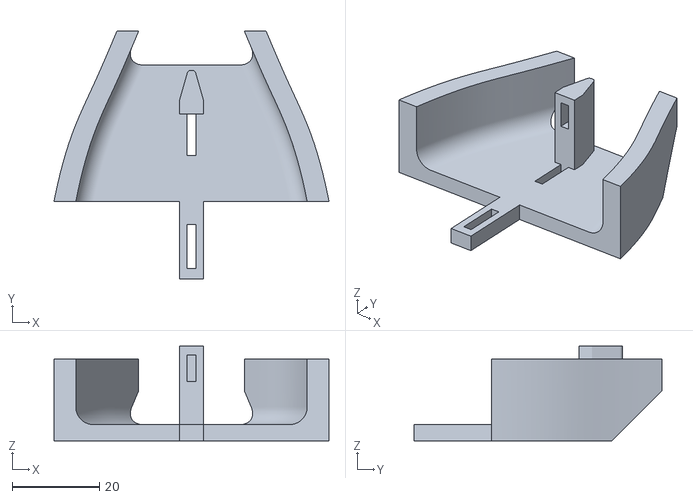
[picture p70: CAD file, 2025-10-04]
Wall Control Small Hook/Park Tool/Park Tool MLP-1.2.stl
63.0 x 56.8 x 21.8
