taylorjsam/3D-Printed-Wall-Control/Printed Snap Hook Hangers/Generic/Socket Drive Accessories/1x 1:4 Drive Male.stl

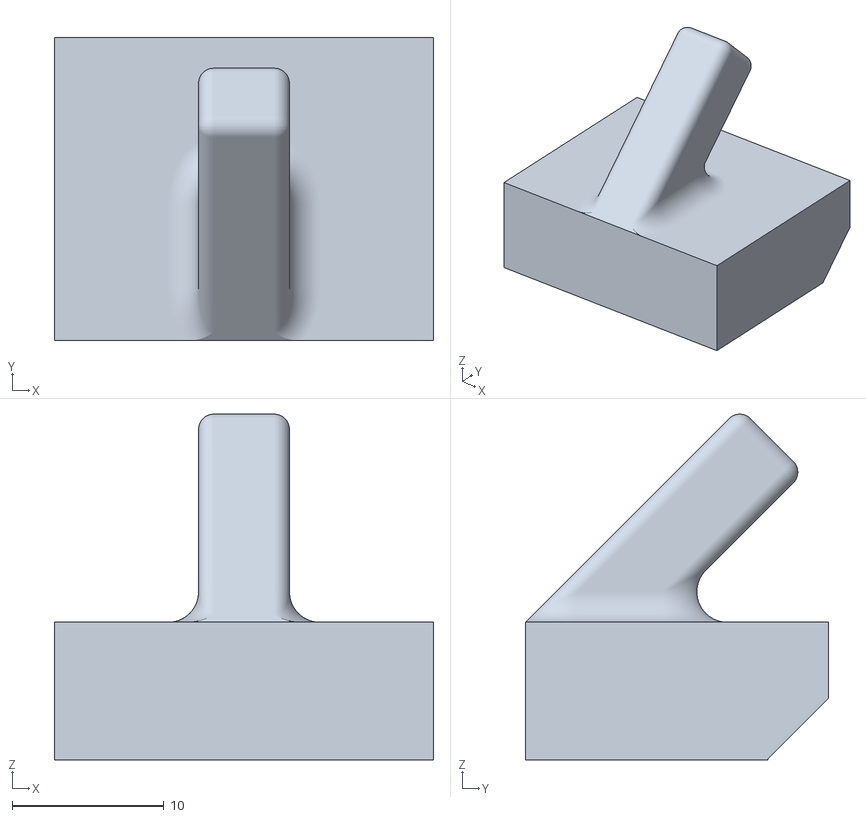
[picture p71: CAD file, 2025-12-20]
Printed Snap Hook Hangers/Generic/Socket Drive Accessories/1x 1:4 Drive Male.stl
25.0 x 20.0 x 22.8
