taylorjsam/3D-Printed-Wall-Control/Printed Snap Hook Hangers/Generic/T Handle Allen 1.5mm (add on) PH.stl

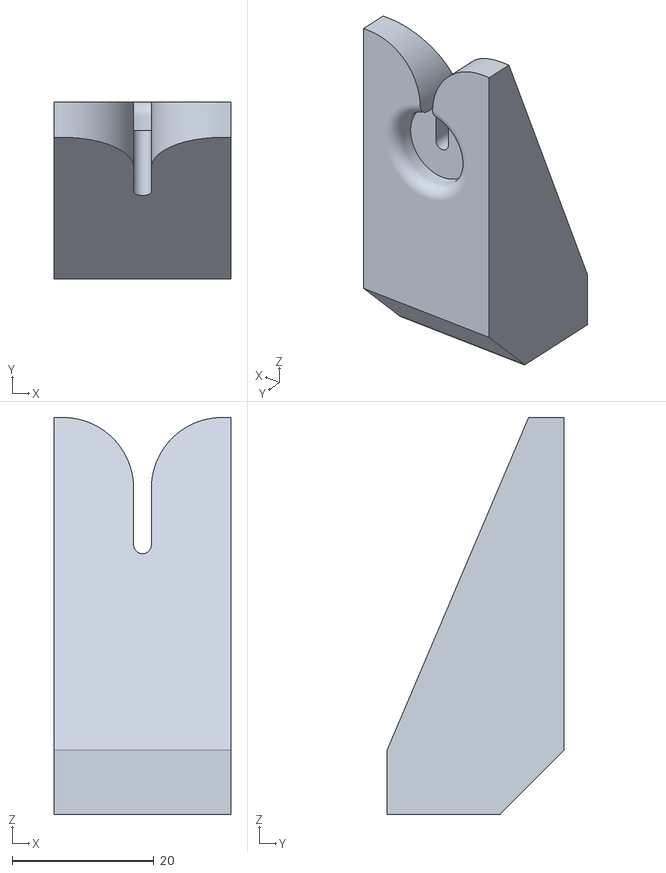
[picture p72: CAD file, 2025-10-18]
Printed Snap Hook Hangers/Generic/T Handle Allen 1.5mm (add on) PH.stl
25.0 x 25.0 x 56.1
