taylorjsam/3D-Printed-Wall-Control/Printed Snap Hook Hangers/Knipex/Knipex 2871280(81) (vert) PH.stl

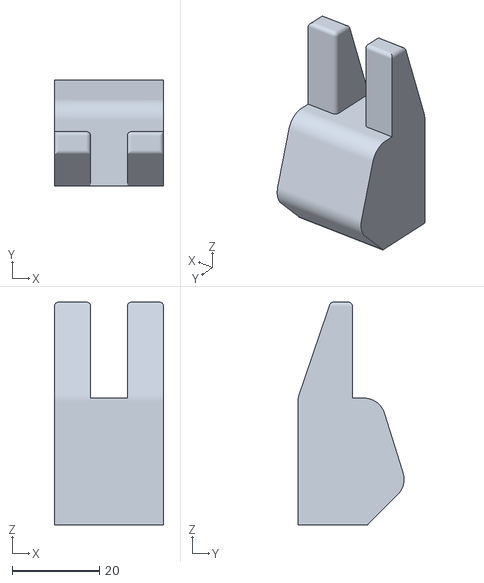
[picture p73: CAD file, 2025-10-23]
Printed Snap Hook Hangers/Knipex/Knipex 2871280(81) (vert) PH.stl
25.0 x 24.3 x 51.1
