taylorjsam/3D-Printed-Wall-Control/Printed Snap Hook Hangers/Milwaukee/Milwaukee 48-22-3406 PH.stl

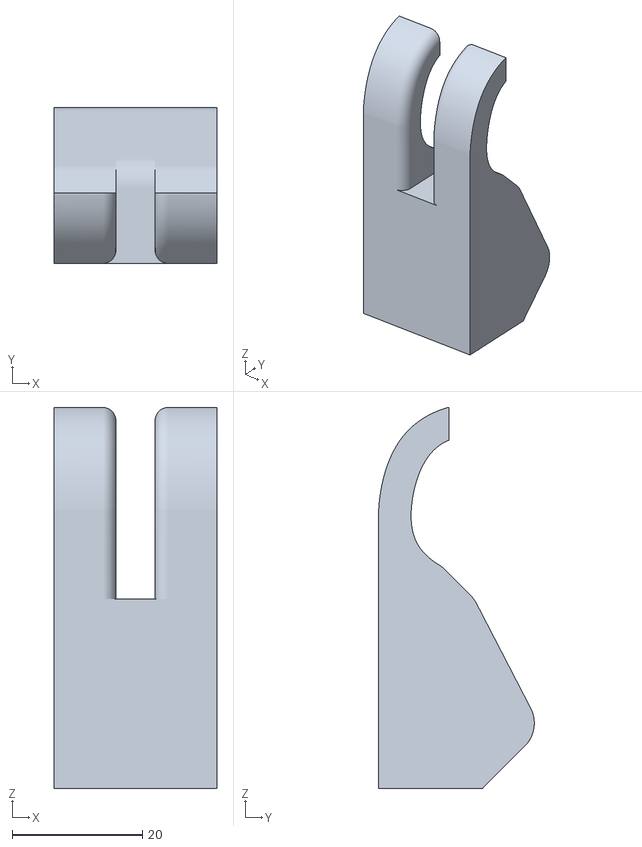
[picture p74: CAD file, 2025-10-24]
Printed Snap Hook Hangers/Milwaukee/Milwaukee 48-22-3406 PH.stl
25.0 x 23.9 x 58.4
