taylorjsam/3D-Printed-Wall-Control/Printed Snap Hook Hangers/Park Tool/Park Tool BT-2 (vert) PH.stl

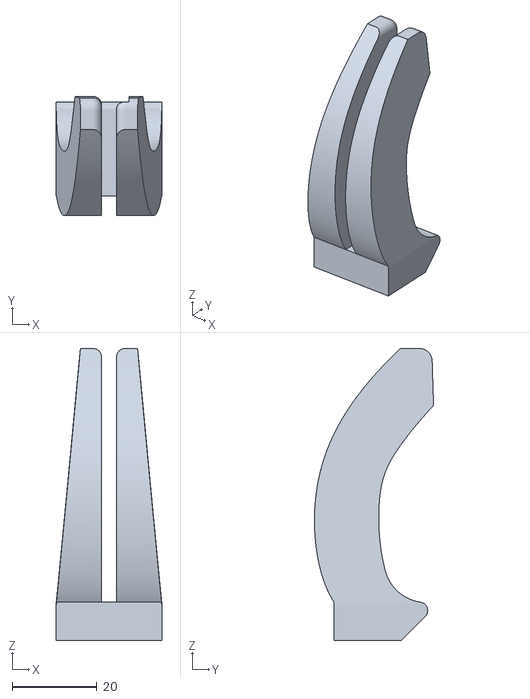
[picture p75: CAD file, 2025-11-06]
Printed Snap Hook Hangers/Park Tool/Park Tool BT-2 (vert) PH.stl
25.0 x 28.2 x 69.1
