taylorjsam/3D-Printed-Wall-Control/Wall Control Small Hook/Park Tool/Park Tool NP-6.stl

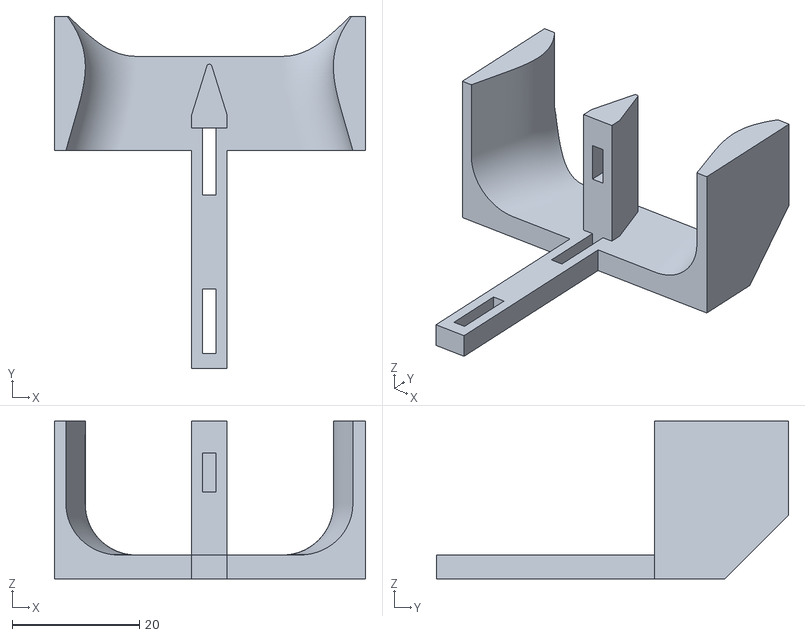
[picture p77: CAD file, 2025-10-04]
Wall Control Small Hook/Park Tool/Park Tool NP-6.stl
48.8 x 55.2 x 24.8
