taylorjsam/3D-Printed-Wall-Control/Printed Snap Hook Hangers/Generic/Bic Ligher Holder PH.stl

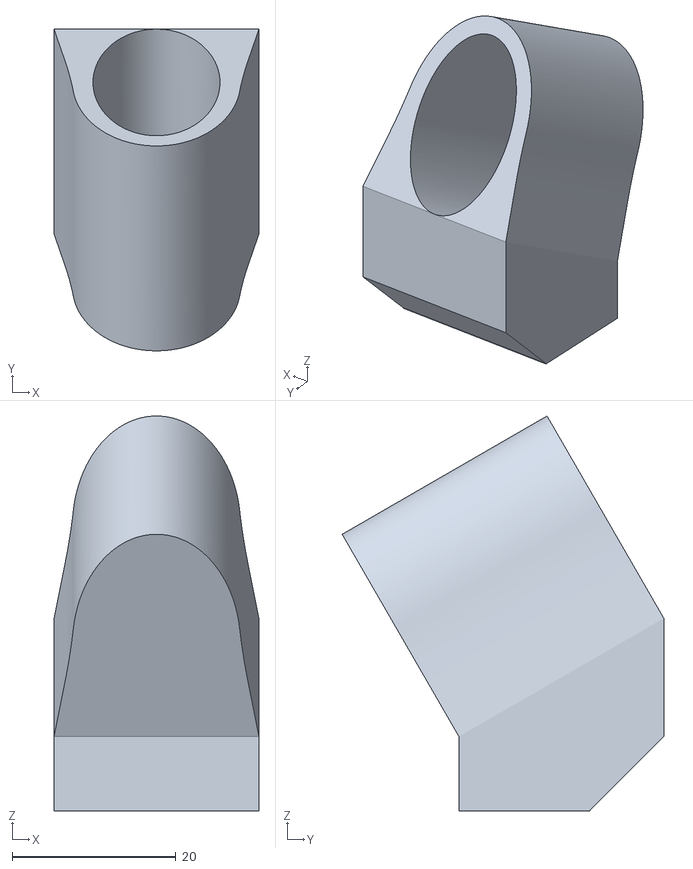
[picture p78: CAD file, 2025-10-18]
Printed Snap Hook Hangers/Generic/Bic Ligher Holder PH.stl
25.0 x 39.3 x 48.2
