taylorjsam/3D-Printed-Wall-Control/Printed Snap Hook Hangers/Generic/Socket Drive Accessories/1:4 Drive Extension.stl

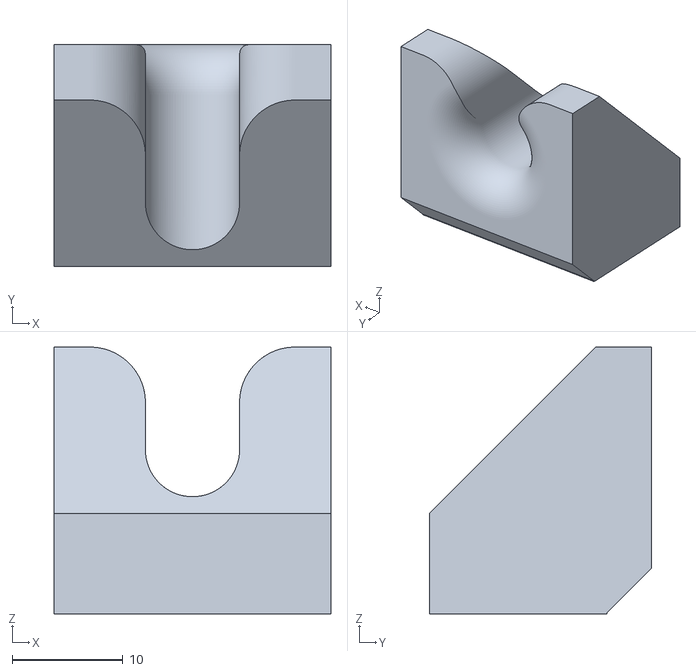
[picture p79: CAD file, 2025-12-20]
Printed Snap Hook Hangers/Generic/Socket Drive Accessories/1:4 Drive Extension.stl
25.0 x 20.0 x 24.1
