taylorjsam/3D-Printed-Wall-Control/Printed Snap Hook Hangers/Knipex/Knipex 9505155 (vert) PH.stl

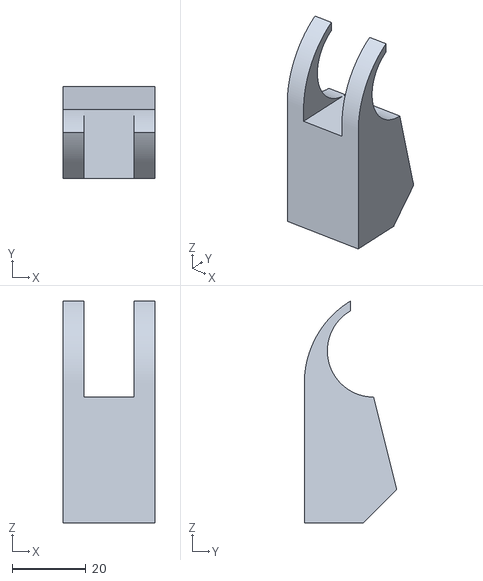
[picture p80: CAD file, 2025-10-23]
Printed Snap Hook Hangers/Knipex/Knipex 9505155 (vert) PH.stl
25.0 x 25.0 x 60.1
