taylorjsam/3D-Printed-Wall-Control/Printed Snap Hook Hangers/Park Tool/Park Tool ATD-1.2 (vert-mount)PH.stl

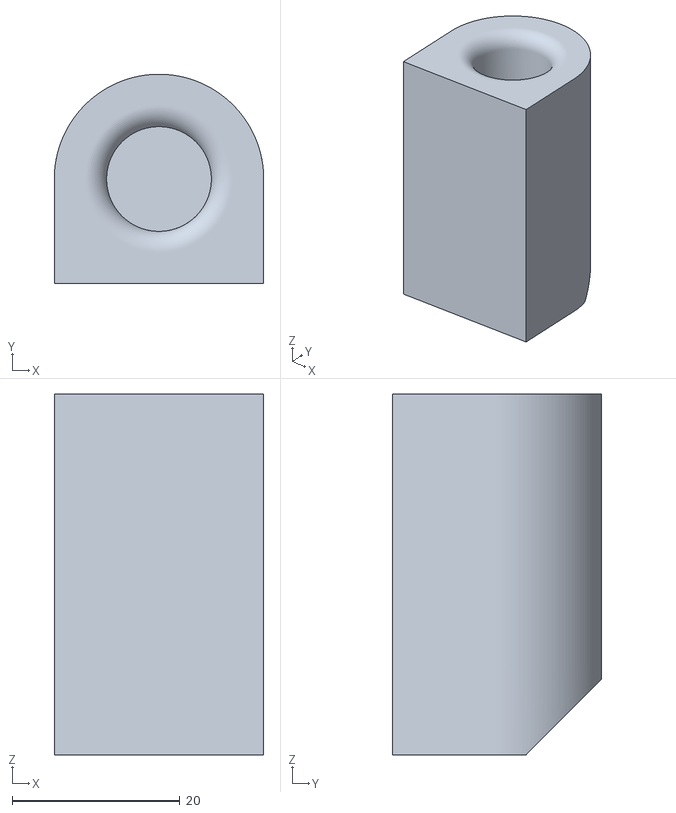
[picture p81: CAD file, 2025-11-05]
Printed Snap Hook Hangers/Park Tool/Park Tool ATD-1.2 (vert-mount)PH.stl
25.0 x 25.0 x 43.1
