taylorjsam/3D-Printed-Wall-Control/Wall Control Small Hook/Generic/Quarter Inch Male Tool Holder.stl

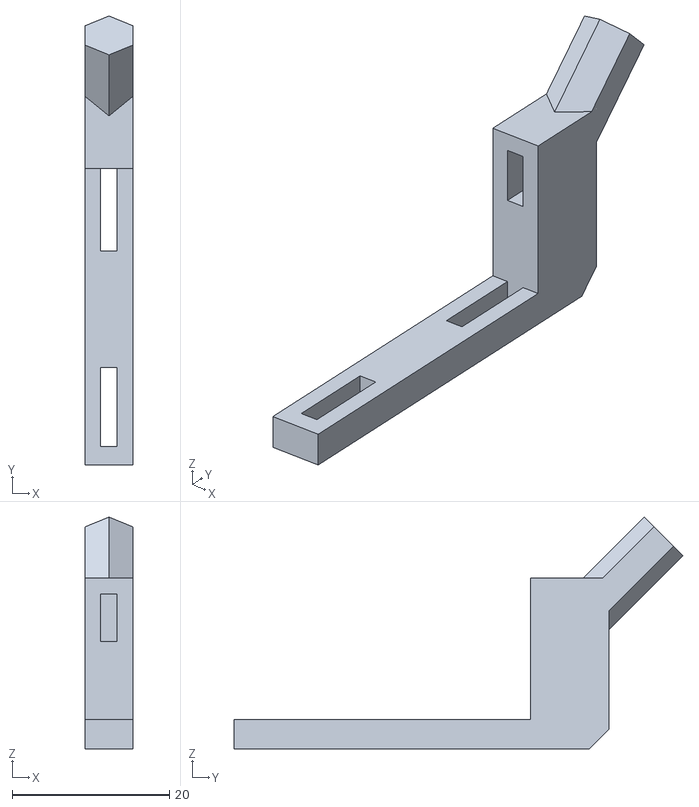
[picture p82: CAD file, 2025-10-04]
Wall Control Small Hook/Generic/Quarter Inch Male Tool Holder.stl
6.08 x 57.2 x 29.5
