taylorjsam/3D-Printed-Wall-Control/Wall Control Small Hook/Park Tool/Park Tool DT-2.stl

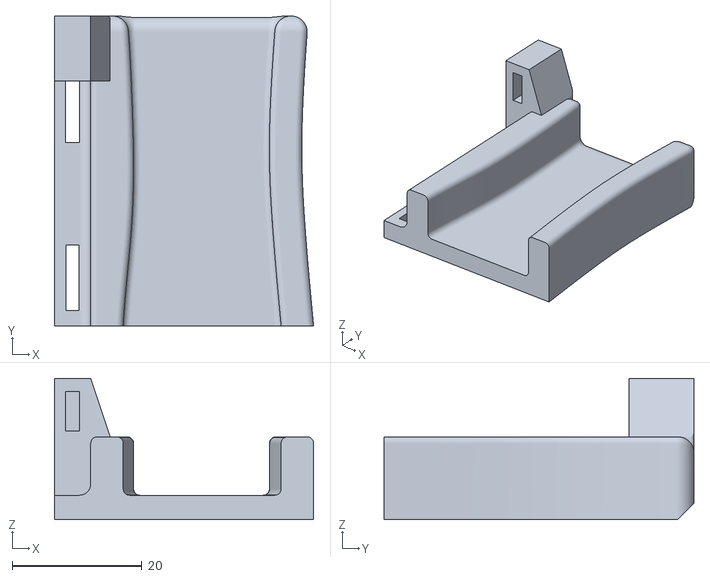
[picture p83: CAD file, 2025-10-04]
Wall Control Small Hook/Park Tool/Park Tool DT-2.stl
39.9 x 47.8 x 21.8
