taylorjsam/3D-Printed-Wall-Control/Printed Snap Hook Hangers/Generic/Triangle Hook 25x25mm PH.stl

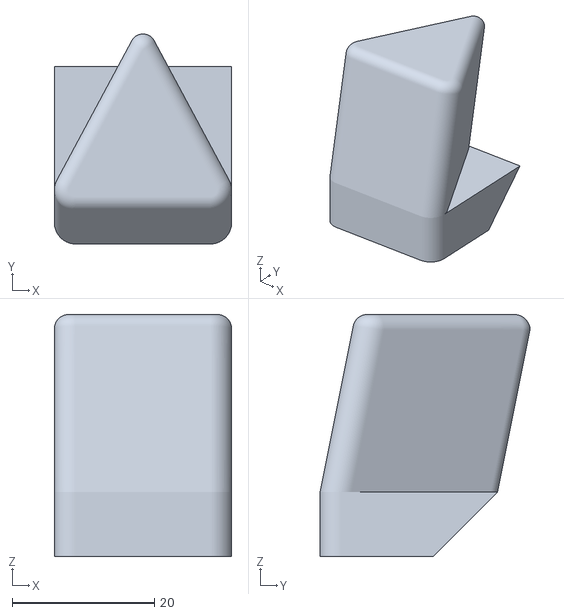
[picture p84: CAD file, 2025-10-10]
Printed Snap Hook Hangers/Generic/Triangle Hook 25x25mm PH.stl
25.0 x 29.6 x 34.1
