taylorjsam/3D-Printed-Wall-Control/Printed Snap Hook Hangers/Knipex/Knipex 8702250 (vert) PH.stl

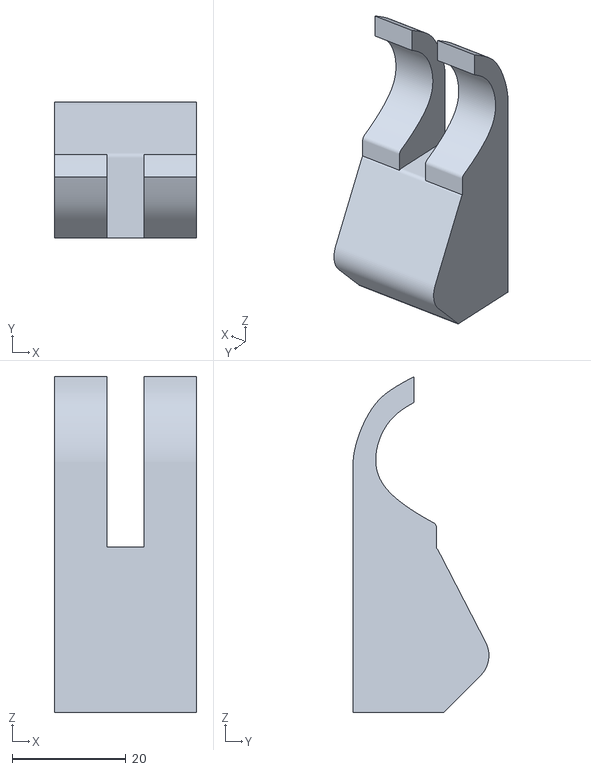
[picture p85: CAD file, 2025-10-23]
Printed Snap Hook Hangers/Knipex/Knipex 8702250 (vert) PH.stl
25.0 x 23.9 x 59.1
