taylorjsam/3D-Printed-Wall-Control/Printed Snap Hook Hangers/Park Tool/Park Tool AWS-1 (Vertical) PH.stl

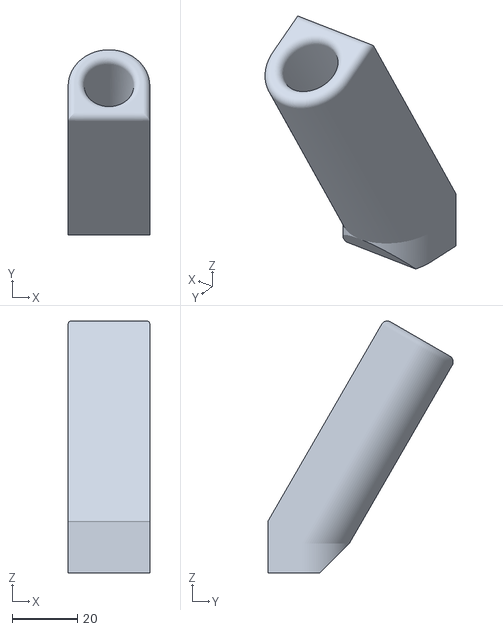
[picture p86: CAD file, 2025-10-23]
Printed Snap Hook Hangers/Park Tool/Park Tool AWS-1 (Vertical) PH.stl
25.0 x 56.8 x 77.1
