taylorjsam/3D-Printed-Wall-Control/Wall Control Small Hook/Park Tool/Park Tool BT-2.stl

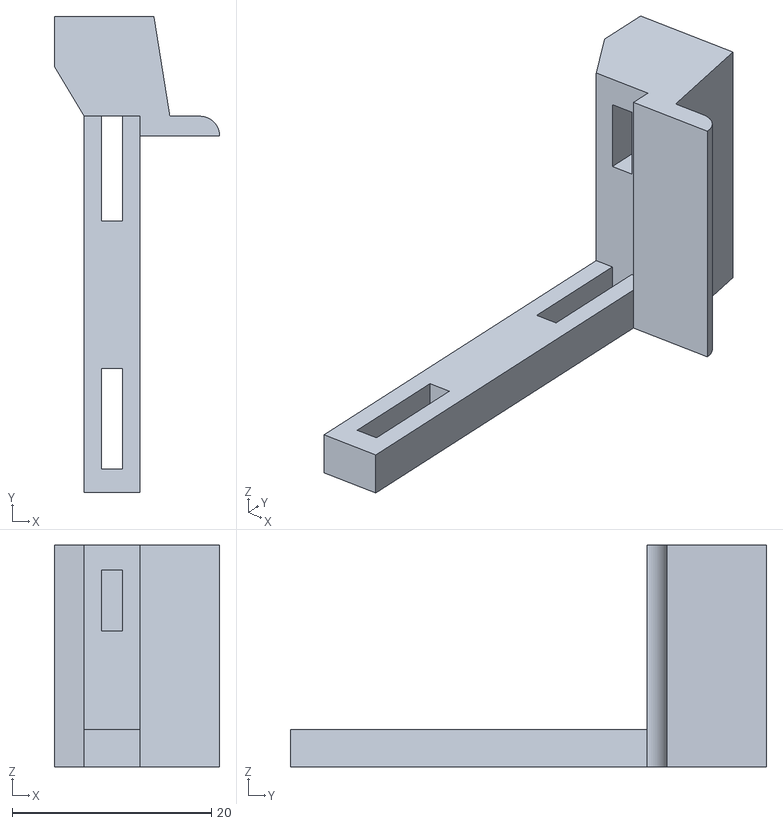
[picture p88: CAD file, 2025-10-04]
Wall Control Small Hook/Park Tool/Park Tool BT-2.stl
16.6 x 47.8 x 22.2
