taylorjsam/3D-Printed-Wall-Control/Printed Snap Hook Hangers/Generic/Flat Hook 25mm at 45deg PH.stl

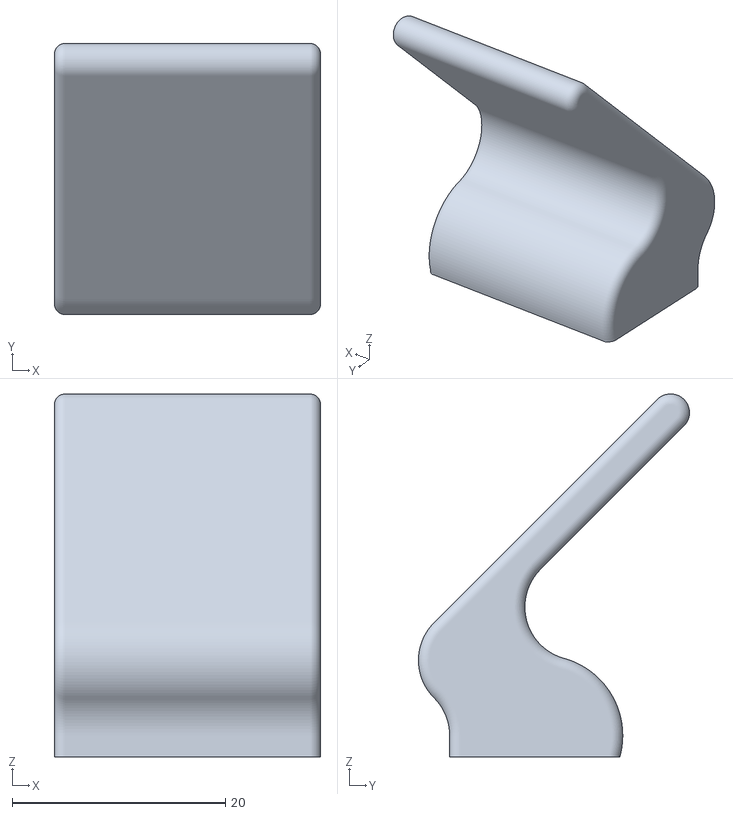
[picture p89: CAD file, 2025-10-10]
Printed Snap Hook Hangers/Generic/Flat Hook 25mm at 45deg PH.stl
25.0 x 25.5 x 34.1
