taylorjsam/3D-Printed-Wall-Control/Printed Snap Hook Hangers/Park Tool/Park Tool MLP-1.2 PH.stl

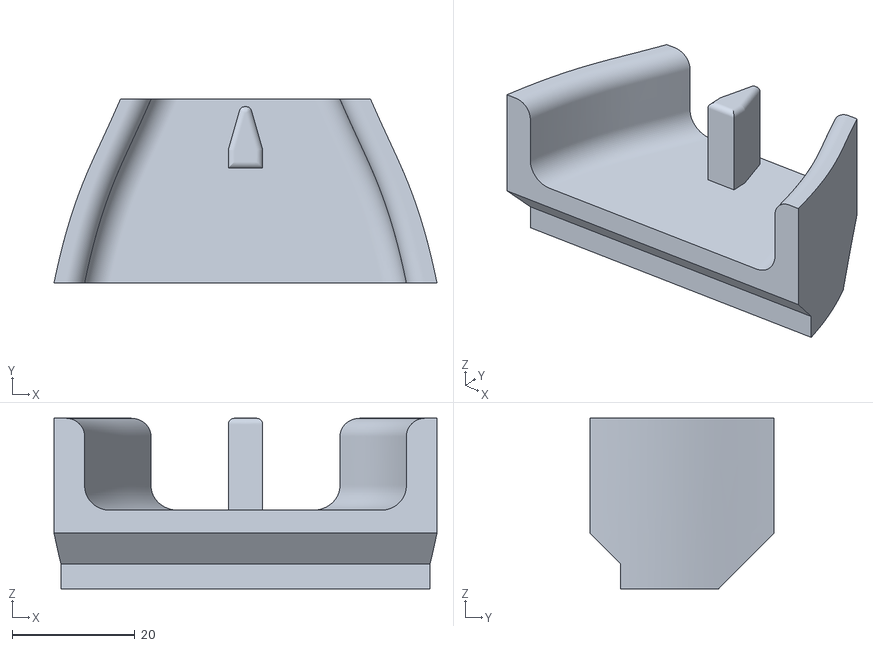
[picture p91: CAD file, 2025-10-19]
Printed Snap Hook Hangers/Park Tool/Park Tool MLP-1.2 PH.stl
62.5 x 30.0 x 27.8
