taylorjsam/3D-Printed-Wall-Control/Wall Control Small Hook/Park Tool/Park Tool CT-3.stl

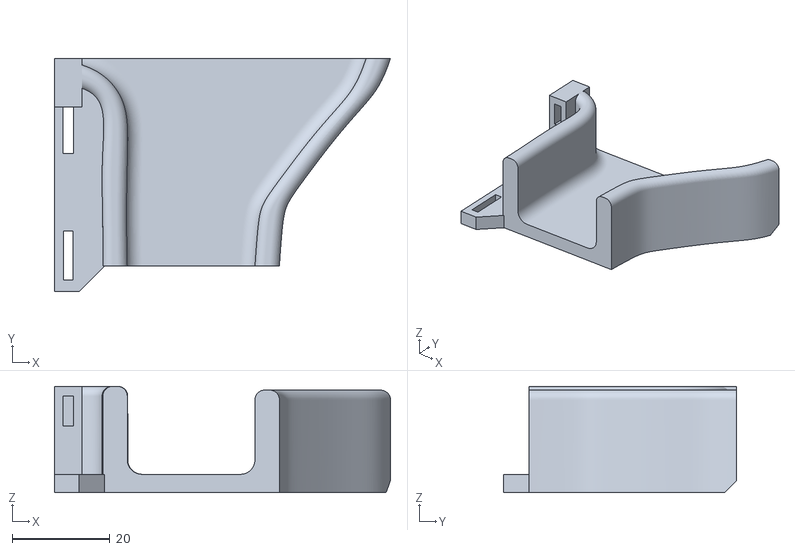
[picture p93: CAD file, 2025-10-04]
Wall Control Small Hook/Park Tool/Park Tool CT-3.stl
68.8 x 47.8 x 21.8
