taylorjsam/3D-Printed-Wall-Control/Printed Snap Hook Hangers/Generic/Spoke Pick Holder PH.stl

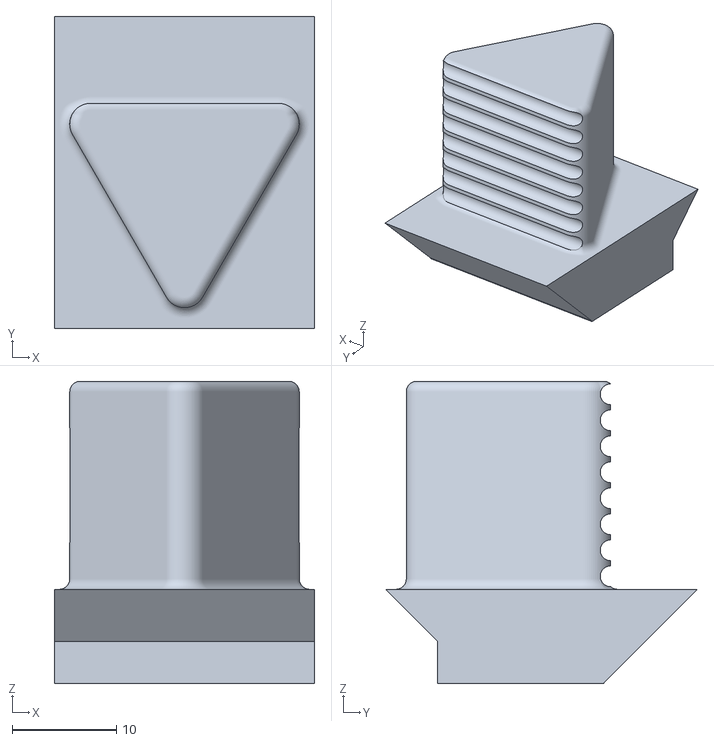
[picture p94: CAD file, 2025-10-09]
Printed Snap Hook Hangers/Generic/Spoke Pick Holder PH.stl
25.0 x 30.0 x 29.1
