taylorjsam/3D-Printed-Wall-Control/Printed Snap Hook Hangers/Park Tool/Park Tool BBT-9 PH.stl

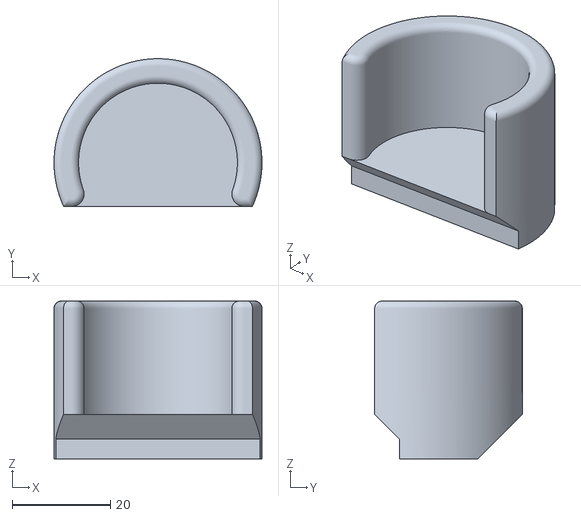
[picture p96: CAD file, 2025-10-19]
Printed Snap Hook Hangers/Park Tool/Park Tool BBT-9 PH.stl
42.2 x 30.0 x 32.1
