taylorjsam/3D-Printed-Wall-Control/Wall Control Small Hook/Generic/25mm (cylinder) v2.stl

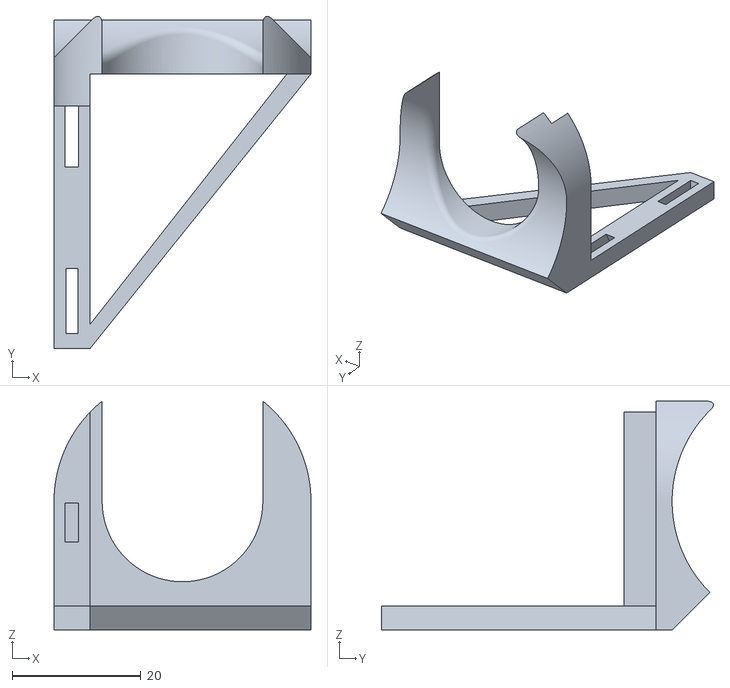
[picture p97: CAD file, 2025-10-04]
Wall Control Small Hook/Generic/25mm (cylinder) v2.stl
40.0 x 51.7 x 35.6
