taylorjsam/3D-Printed-Wall-Control/Printed Snap Hook Hangers/Generic/Calipers (shallow) PH.stl

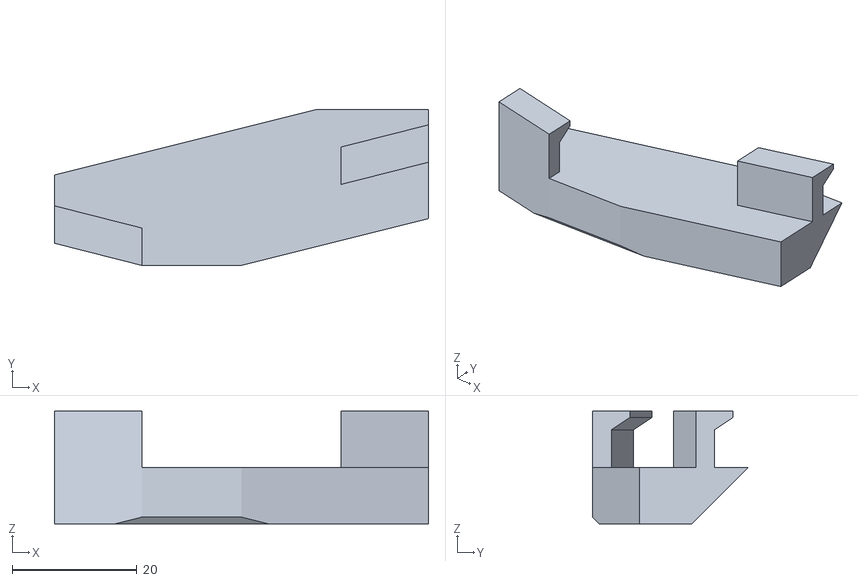
[picture p98: CAD file, 2025-10-08]
Printed Snap Hook Hangers/Generic/Calipers (shallow) PH.stl
60.0 x 25.0 x 18.1
