taylorjsam/3D-Printed-Wall-Control/Printed Snap Hook Hangers/Park Tool/Park Tool NP-6 PH.stl

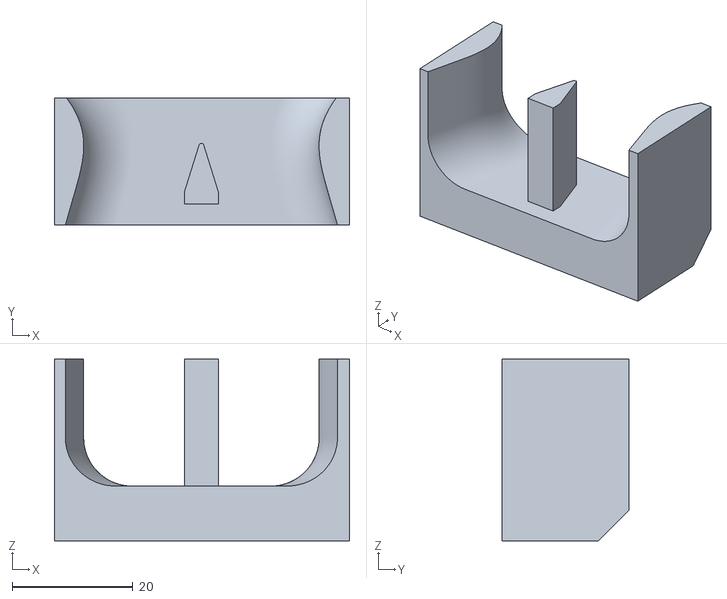
[picture p100: CAD file, 2025-10-18]
Printed Snap Hook Hangers/Park Tool/Park Tool NP-6 PH.stl
48.8 x 21.0 x 30.1
