taylorjsam/3D-Printed-Wall-Control/Wall Control Small Hook/Generic/10mm (chamfered) v2.stl

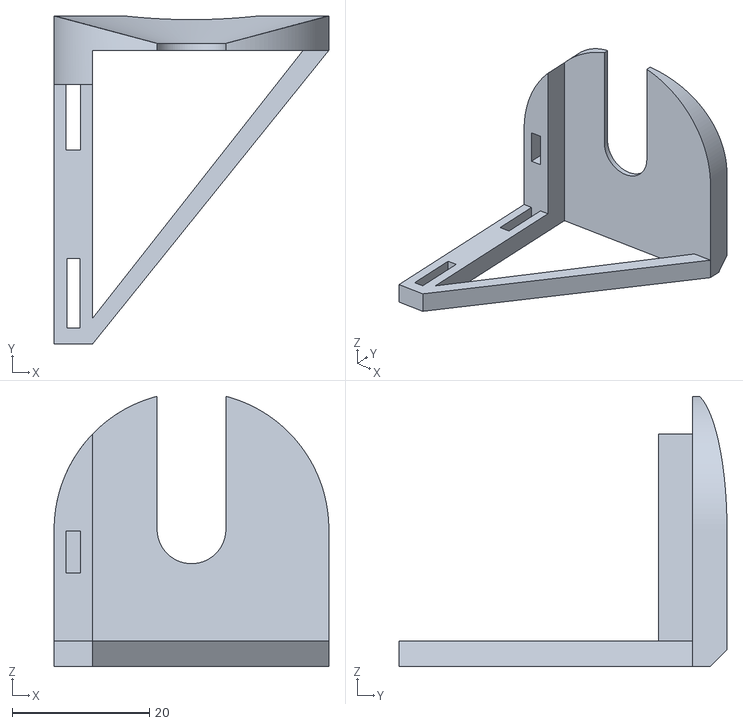
[picture p101: CAD file, 2025-10-04]
Wall Control Small Hook/Generic/10mm (chamfered) v2.stl
40.0 x 47.8 x 39.4
