taylorjsam/3D-Printed-Wall-Control/Printed Snap Hook Hangers/Park Tool/Park Tool PH-1.2 PH.stl

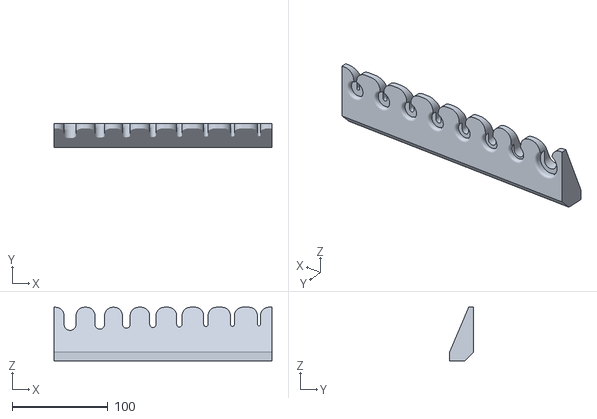
[picture p102: CAD file, 2025-10-18]
Printed Snap Hook Hangers/Park Tool/Park Tool PH-1.2 PH.stl
228.2 x 25.0 x 56.1
