taylorjsam/3D-Printed-Wall-Control/Wall Control Small Hook/Generic/10mm (cylinder) v2.stl

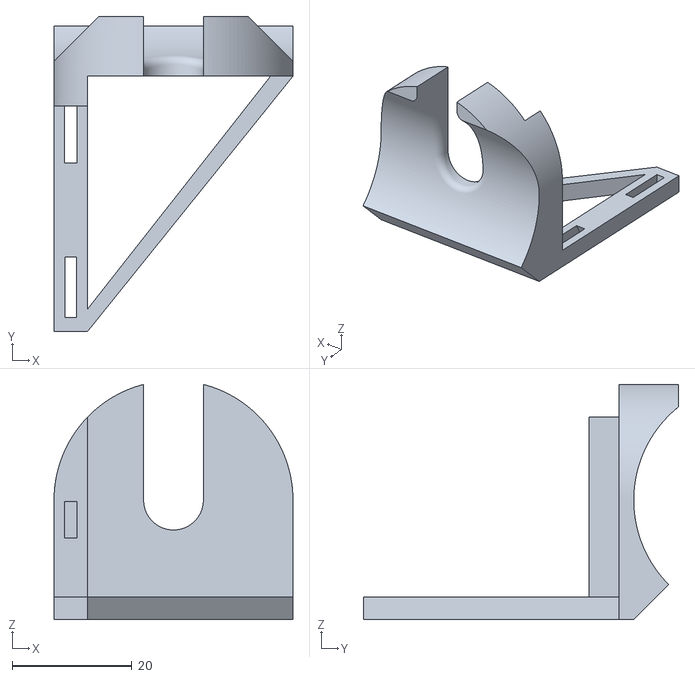
[picture p103: CAD file, 2025-10-04]
Wall Control Small Hook/Generic/10mm (cylinder) v2.stl
40.0 x 52.8 x 39.4
