taylorjsam/3D-Printed-Wall-Control/Printed Snap Hook Hangers/Knipex/Knipex 8202200 (vert) PH.stl

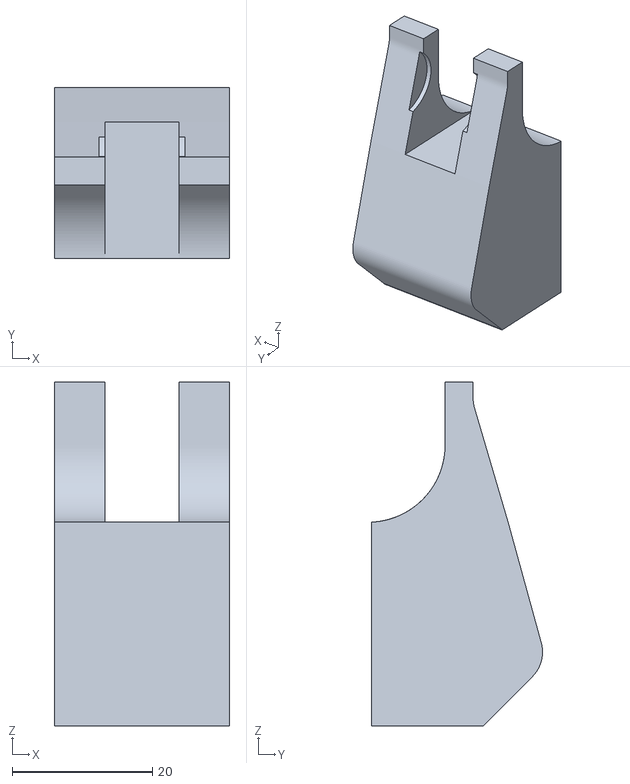
[picture p104: CAD file, 2025-10-23]
Printed Snap Hook Hangers/Knipex/Knipex 8202200 (vert) PH.stl
25.0 x 24.4 x 49.1
