taylorjsam/3D-Printed-Wall-Control/Printed Snap Hook Hangers/Park Tool/Park Tool CCP-22 PH.stl

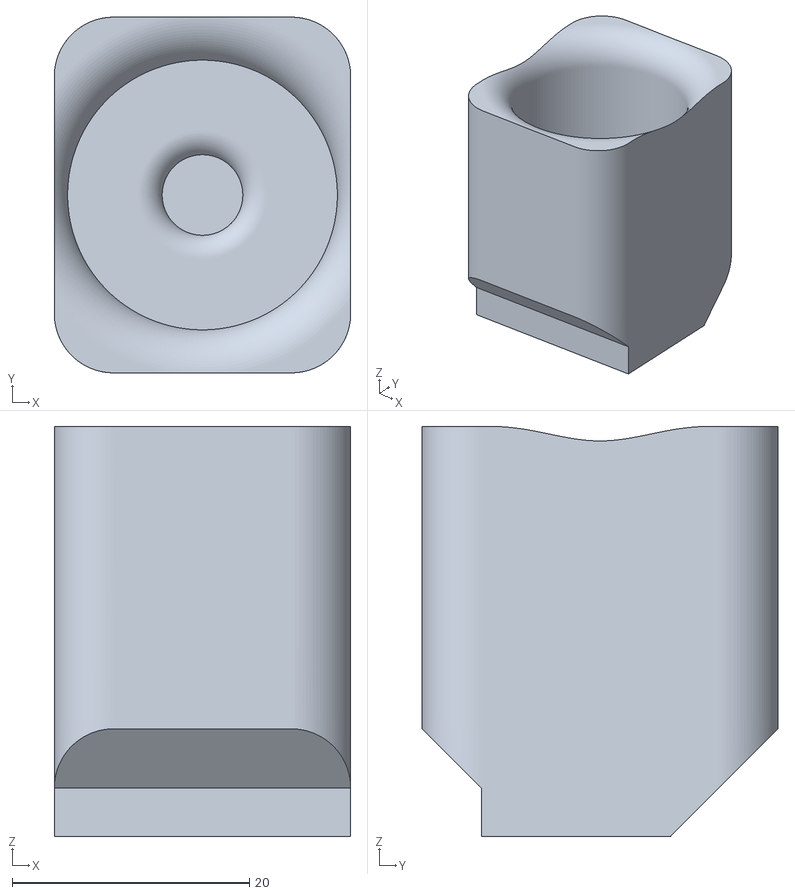
[picture p105: CAD file, 2025-10-18]
Printed Snap Hook Hangers/Park Tool/Park Tool CCP-22 PH.stl
25.0 x 30.0 x 34.6
