taylorjsam/3D-Printed-Wall-Control/Printed Snap Hook Hangers/Knipex/Knipex 8602180 (vert) PH.stl

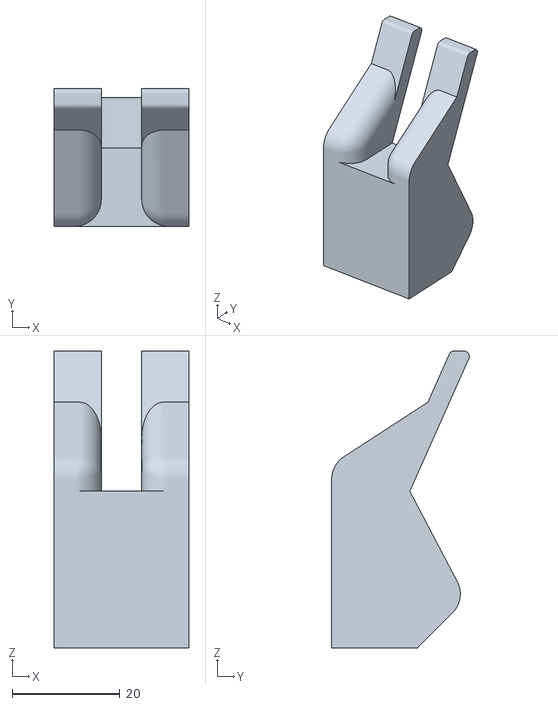
[picture p107: CAD file, 2025-10-23]
Printed Snap Hook Hangers/Knipex/Knipex 8602180 (vert) PH.stl
25.0 x 25.5 x 55.1
