taylorjsam/3D-Printed-Wall-Control/Printed Snap Hook Hangers/Park Tool/Park Tool BT-2 PH.stl

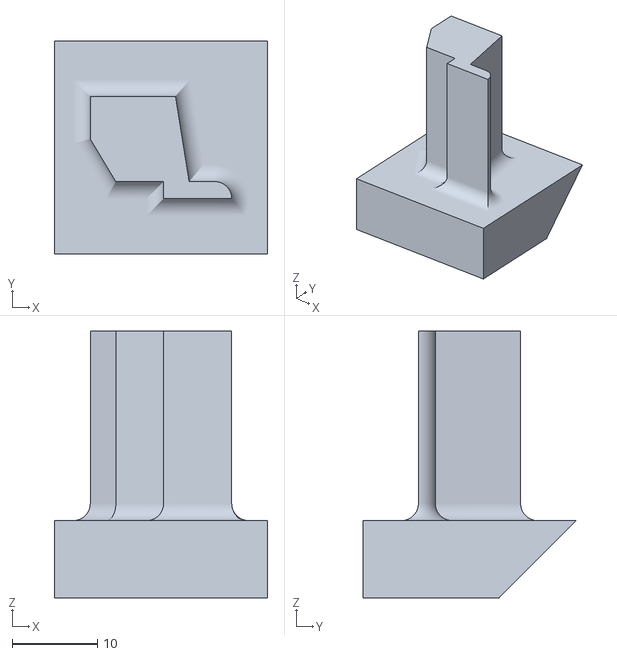
[picture p108: CAD file, 2025-10-18]
Printed Snap Hook Hangers/Park Tool/Park Tool BT-2 PH.stl
25.0 x 25.0 x 31.3
