taylorjsam/3D-Printed-Wall-Control/Printed Snap Hook Hangers/Knipex/Knipex 8702300 (vert) PH.stl

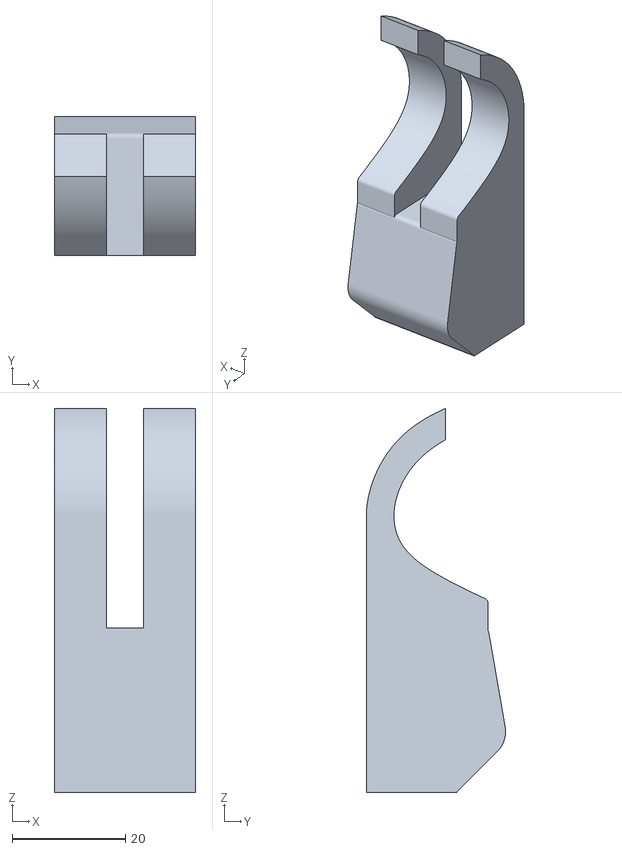
[picture p110: CAD file, 2025-10-23]
Printed Snap Hook Hangers/Knipex/Knipex 8702300 (vert) PH.stl
25.0 x 24.6 x 68.0
