taylorjsam/3D-Printed-Wall-Control/Wall Control Small Hook/Generic/25mm (flat) v2.stl

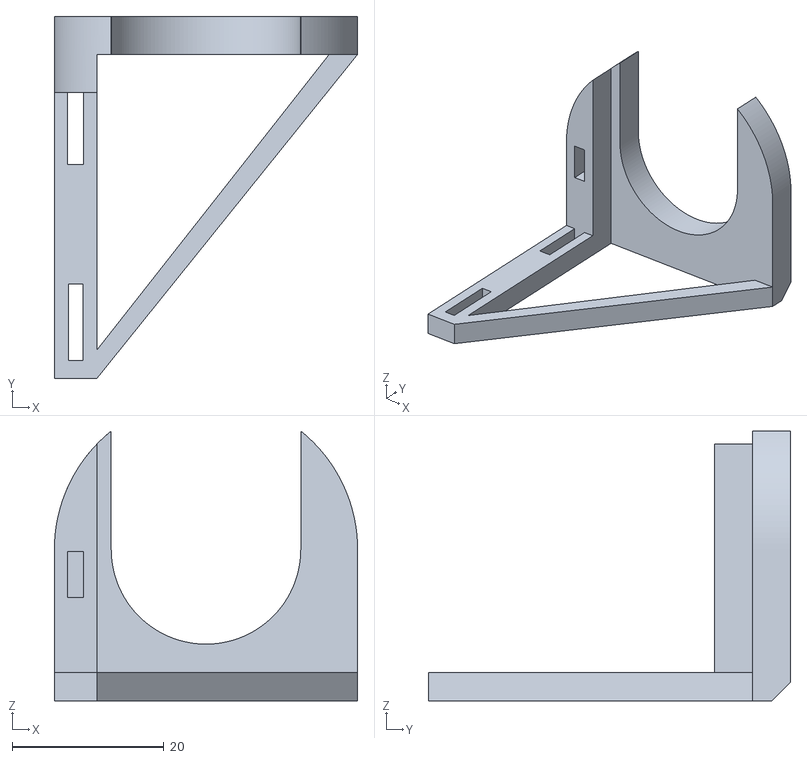
[picture p111: CAD file, 2025-10-04]
Wall Control Small Hook/Generic/25mm (flat) v2.stl
40.0 x 47.8 x 35.6
