taylorjsam/3D-Printed-Wall-Control/Printed Snap Hook Hangers/Park Tool/Park Tool CCW-5 PH.stl

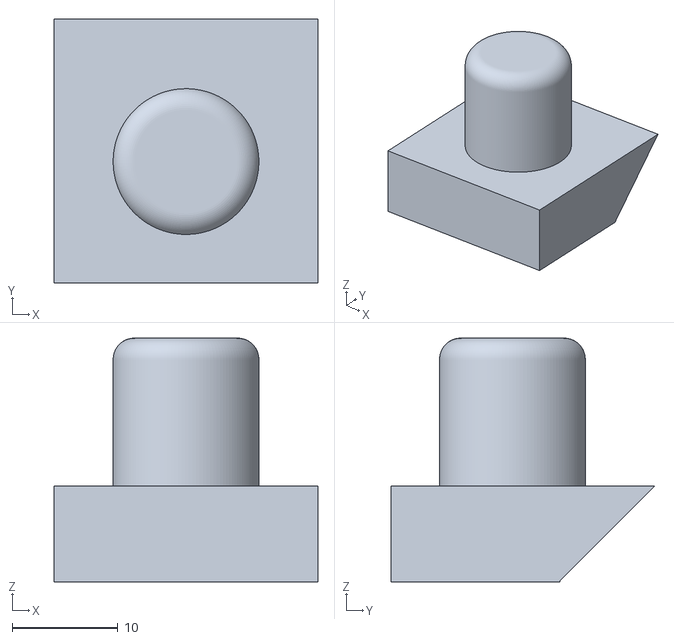
[picture p112: CAD file, 2025-10-08]
Printed Snap Hook Hangers/Park Tool/Park Tool CCW-5 PH.stl
25.0 x 25.0 x 23.1
