taylorjsam/3D-Printed-Wall-Control/Printed Snap Hook Hangers/Park Tool/Park Tool CC-3.2 PH.stl

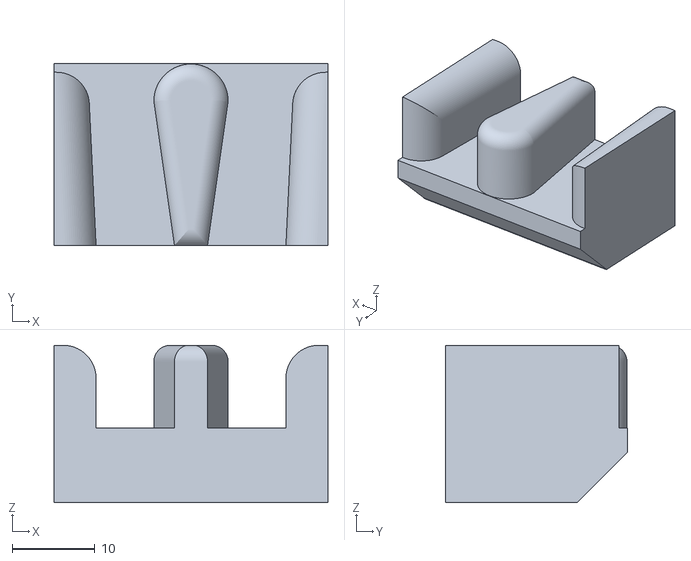
[picture p114: CAD file, 2025-10-08]
Printed Snap Hook Hangers/Park Tool/Park Tool CC-3.2 PH.stl
33.2 x 22.1 x 19.1
