taylorjsam/3D-Printed-Wall-Control/Wall Control Small Hook/Generic/30mm (cylinder) v2.stl

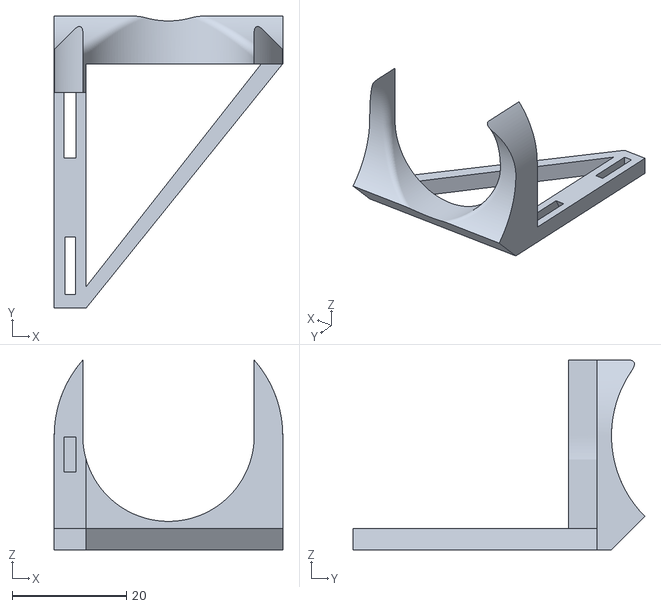
[picture p115: CAD file, 2025-10-04]
Wall Control Small Hook/Generic/30mm (cylinder) v2.stl
40.0 x 51.1 x 33.2
