taylorjsam/3D-Printed-Wall-Control/Printed Snap Hook Hangers/Park Tool/Park Tool CNW-2 PH.stl

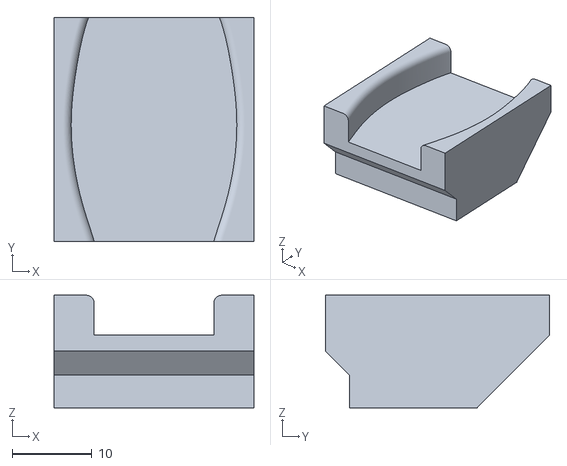
[picture p116: CAD file, 2025-10-08]
Printed Snap Hook Hangers/Park Tool/Park Tool CNW-2 PH.stl
25.0 x 28.0 x 14.1
