taylorjsam/3D-Printed-Wall-Control/Printed Snap Hook Hangers/Park Tool/Park Tool 1in Hex Holder PH.stl

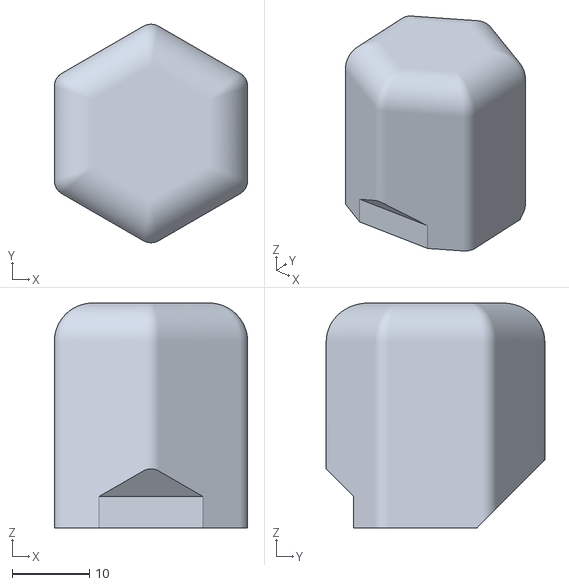
[picture p117: CAD file, 2025-10-08]
Printed Snap Hook Hangers/Park Tool/Park Tool 1in Hex Holder PH.stl
25.0 x 28.2 x 29.1
