taylorjsam/3D-Printed-Wall-Control/Printed Snap Hook Hangers/Park Tool/Park Tool TM-1 PH.stl

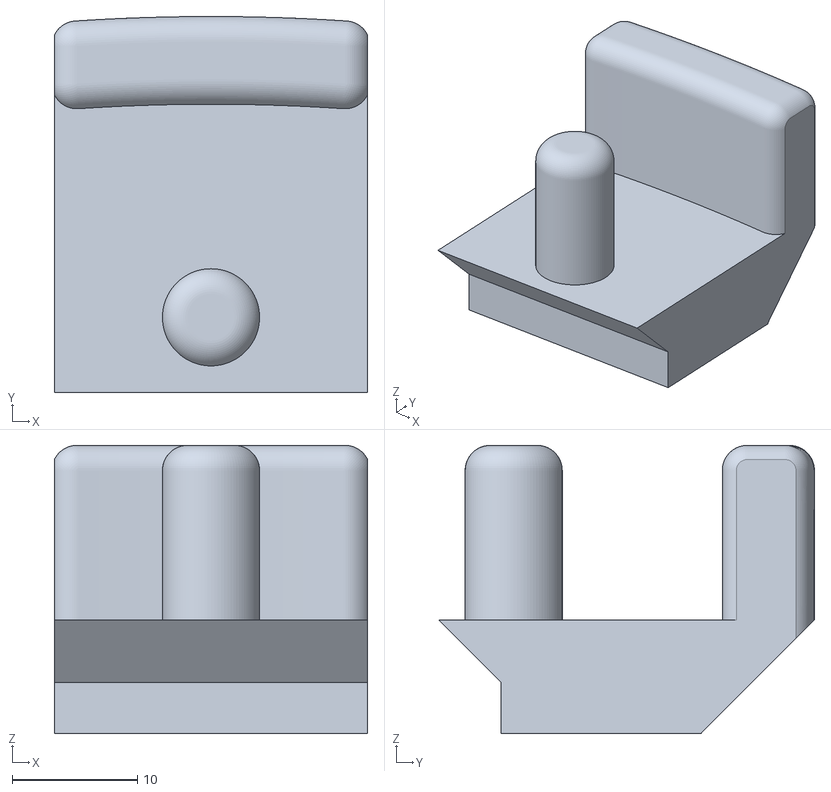
[picture p119: CAD file, 2025-10-08]
Printed Snap Hook Hangers/Park Tool/Park Tool TM-1 PH.stl
25.0 x 30.0 x 23.0
