taylorjsam/3D-Printed-Wall-Control/Wall Control Small Hook/Generic/30mm (chamfered) v2.stl

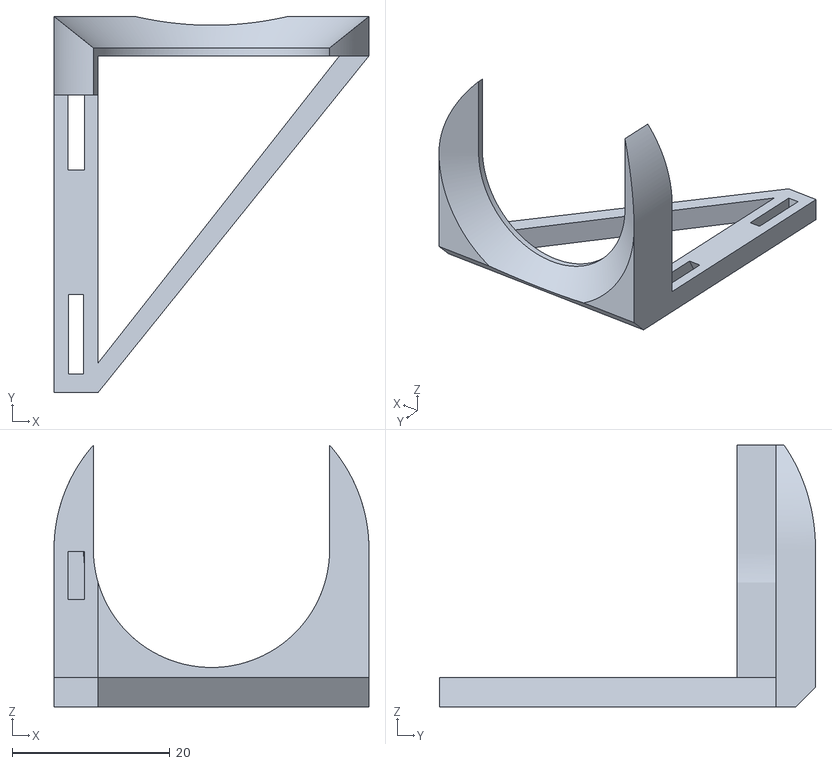
[picture p120: CAD file, 2025-10-04]
Wall Control Small Hook/Generic/30mm (chamfered) v2.stl
40.0 x 47.8 x 33.2
